kevinmfox/8-bit-computer/images/alu01.jpg

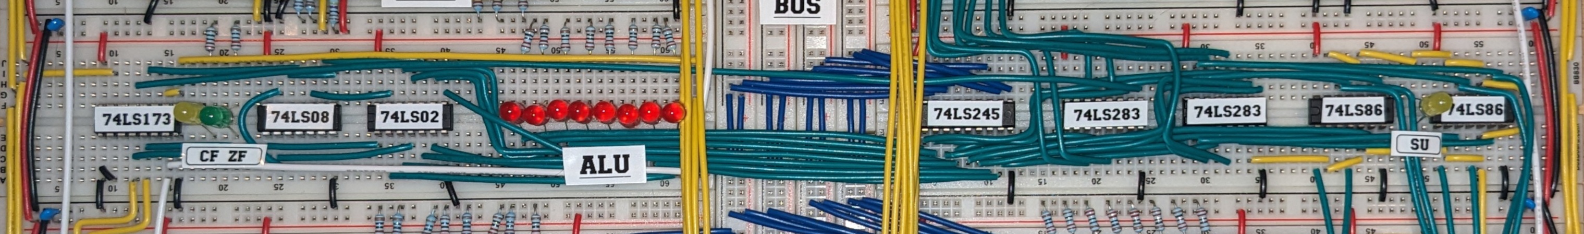
images/alu01.jpg
