kevinmfox/8-bit-computer/images/alu_and_flags01.jpg

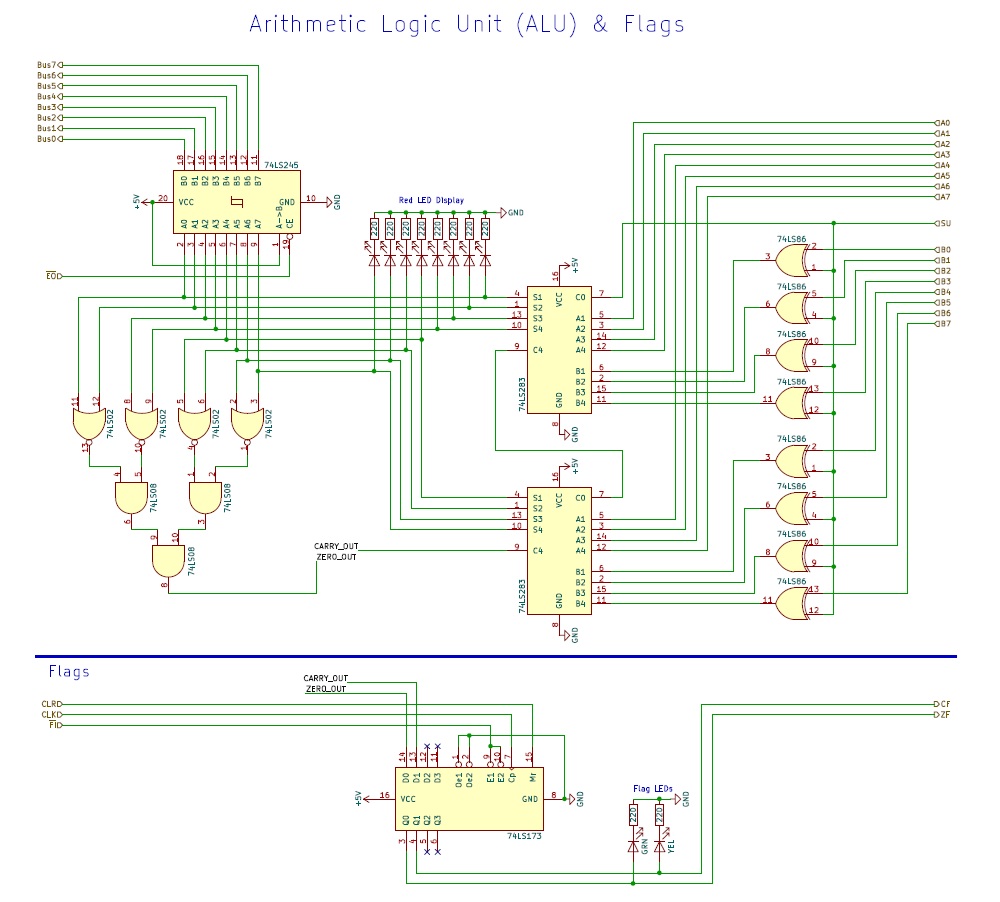
images/alu_and_flags01.jpg
