kevinmfox/8-bit-computer/images/alu_full01.jpg

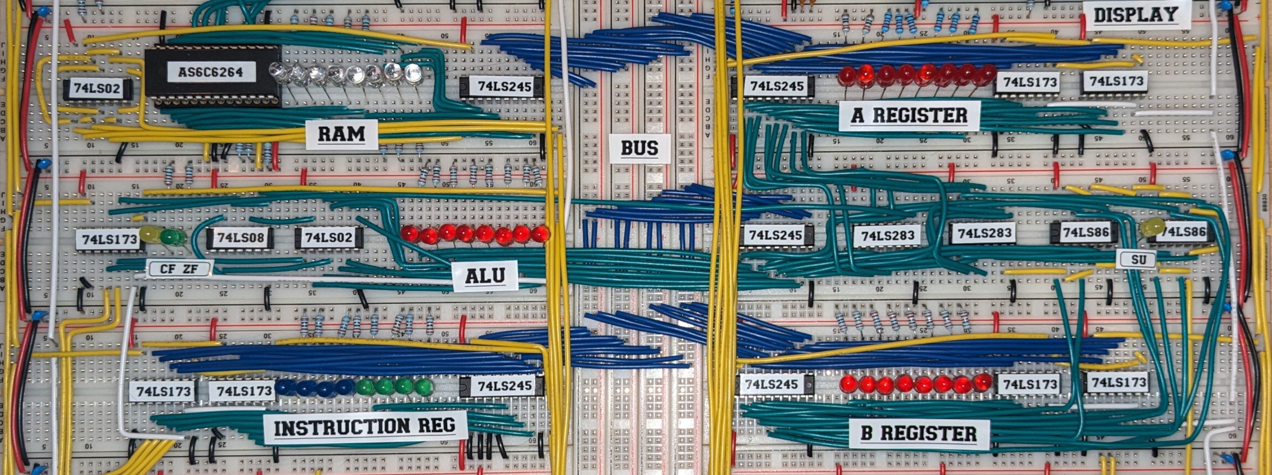
images/alu_full01.jpg
