kevinmfox/8-bit-computer/images/alu_left01.jpg

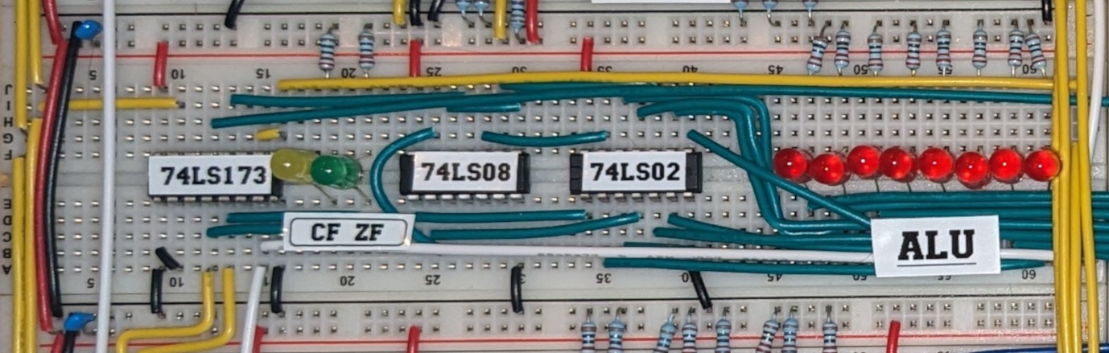
images/alu_left01.jpg
