kevinmfox/8-bit-computer/images/alu_right01.jpg

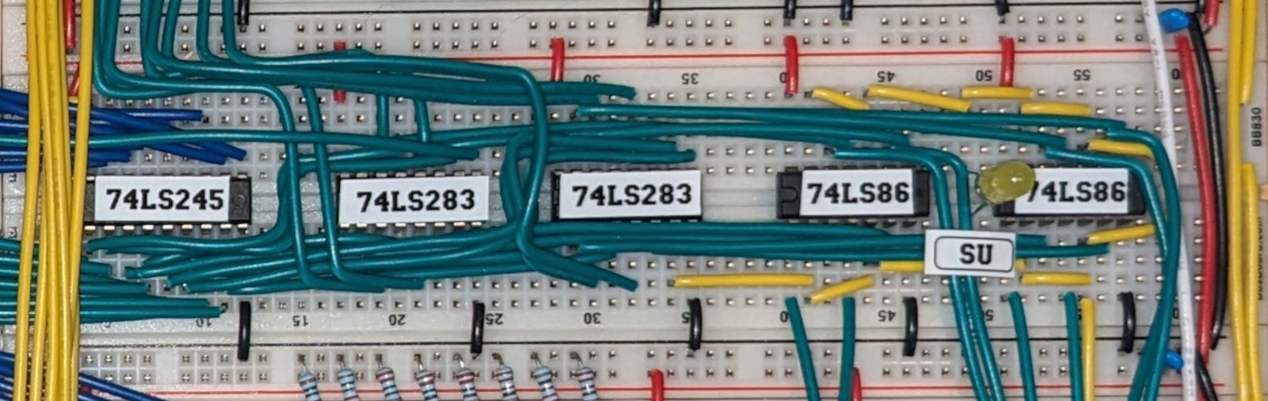
images/alu_right01.jpg
