kevinmfox/8-bit-computer/images/clock01.jpg

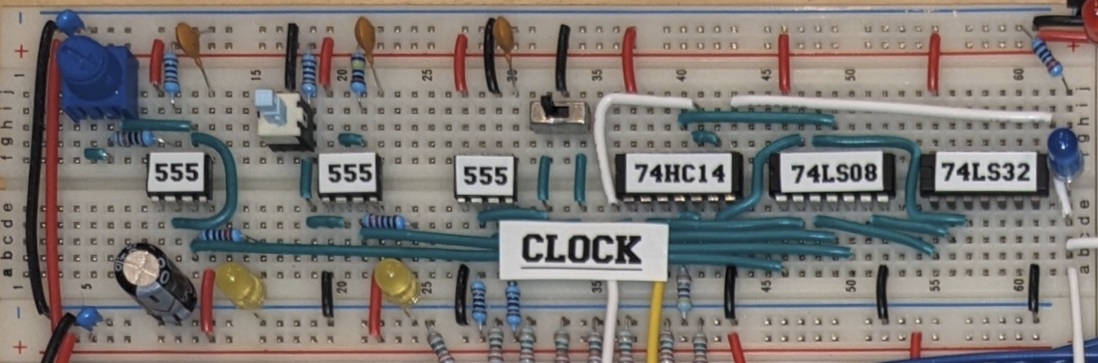
images/clock01.jpg
