kevinmfox/8-bit-computer/images/control01.jpg

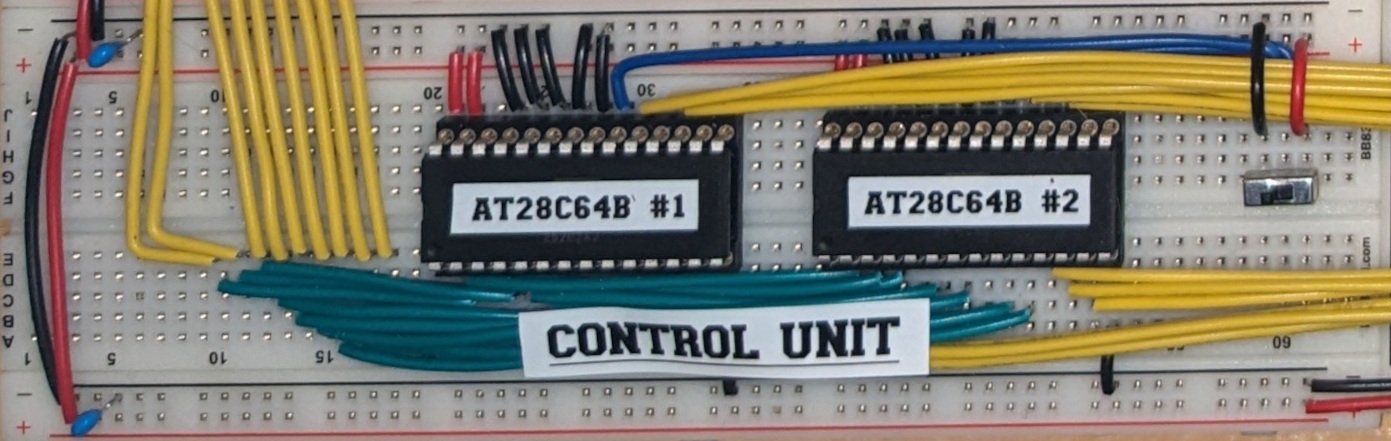
images/control01.jpg
