kevinmfox/8-bit-computer/images/control_leds01.jpg

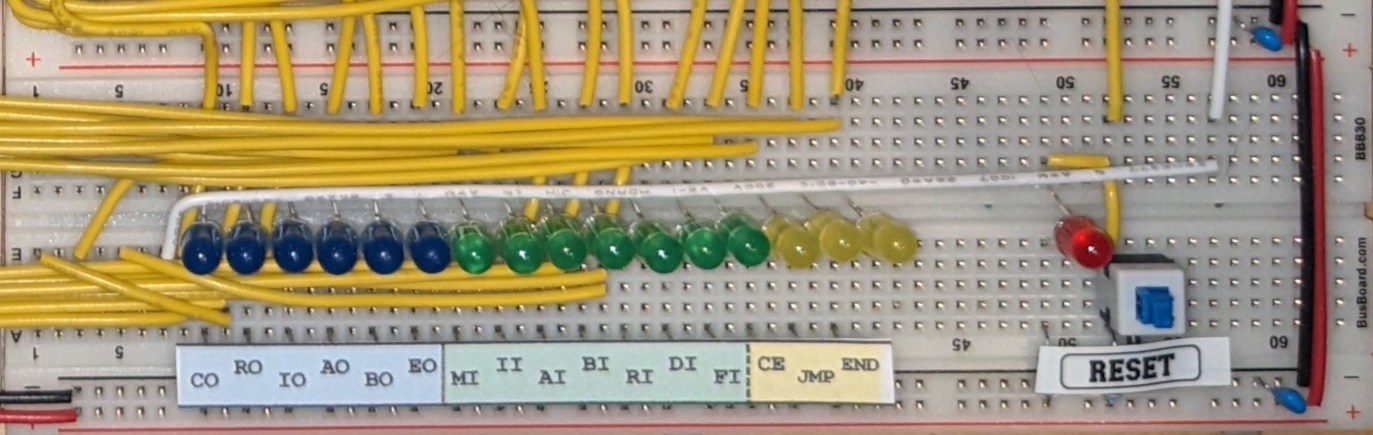
images/control_leds01.jpg
