kevinmfox/8-bit-computer/images/display01.jpg

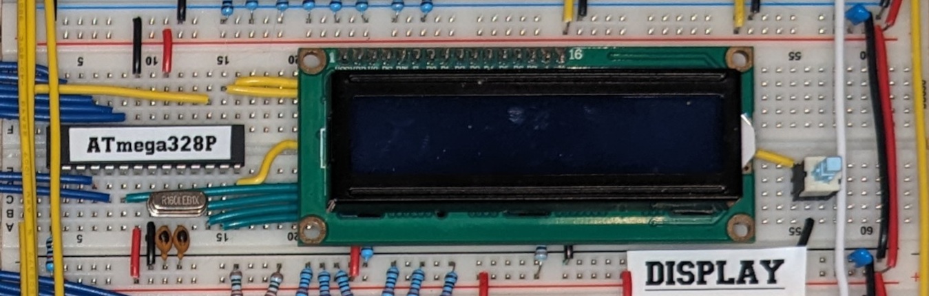
images/display01.jpg
