kevinmfox/8-bit-computer/images/display04.jpg

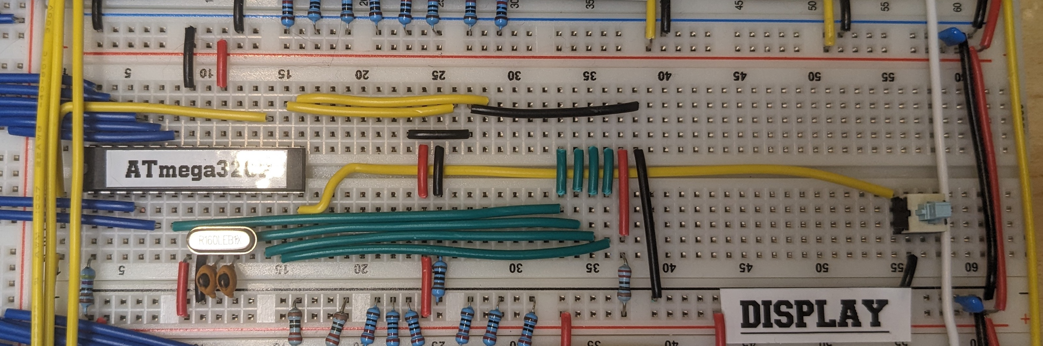
images/display04.jpg
