kevinmfox/8-bit-computer/images/ir01.jpg

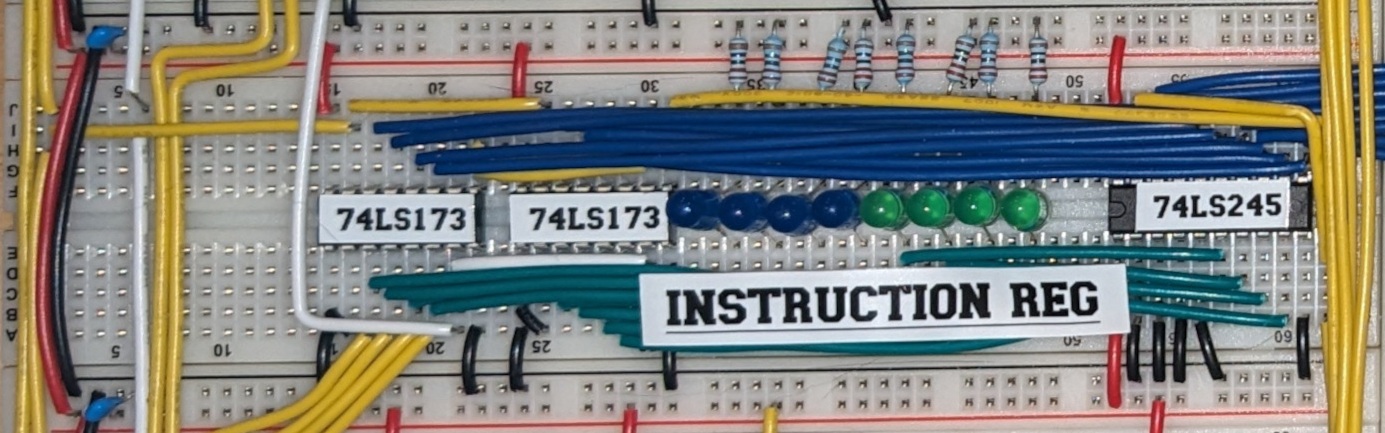
images/ir01.jpg
