kevinmfox/8-bit-computer/images/mar01.jpg

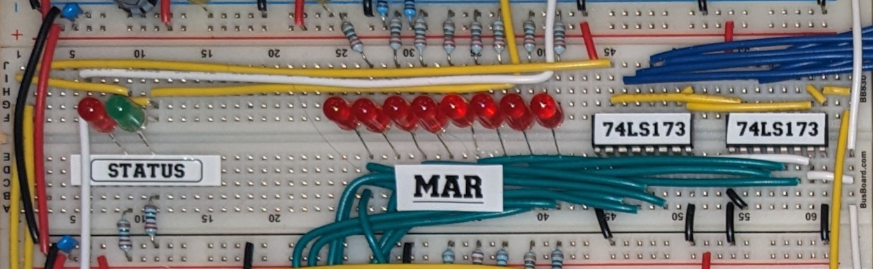
images/mar01.jpg
