kevinmfox/8-bit-computer/images/ram01.jpg

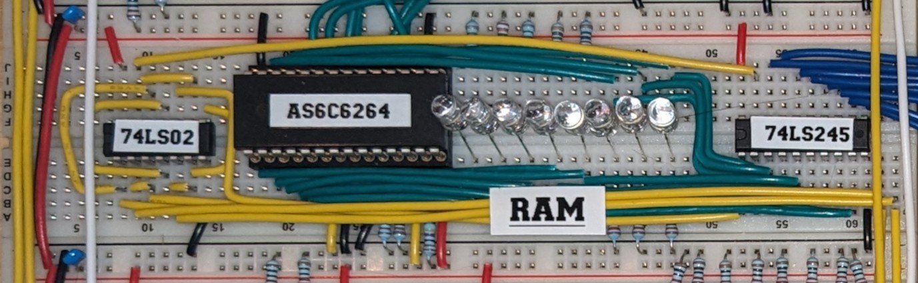
images/ram01.jpg
