kevinmfox/8-bit-computer/images/ram_programmer_sch01.jpg

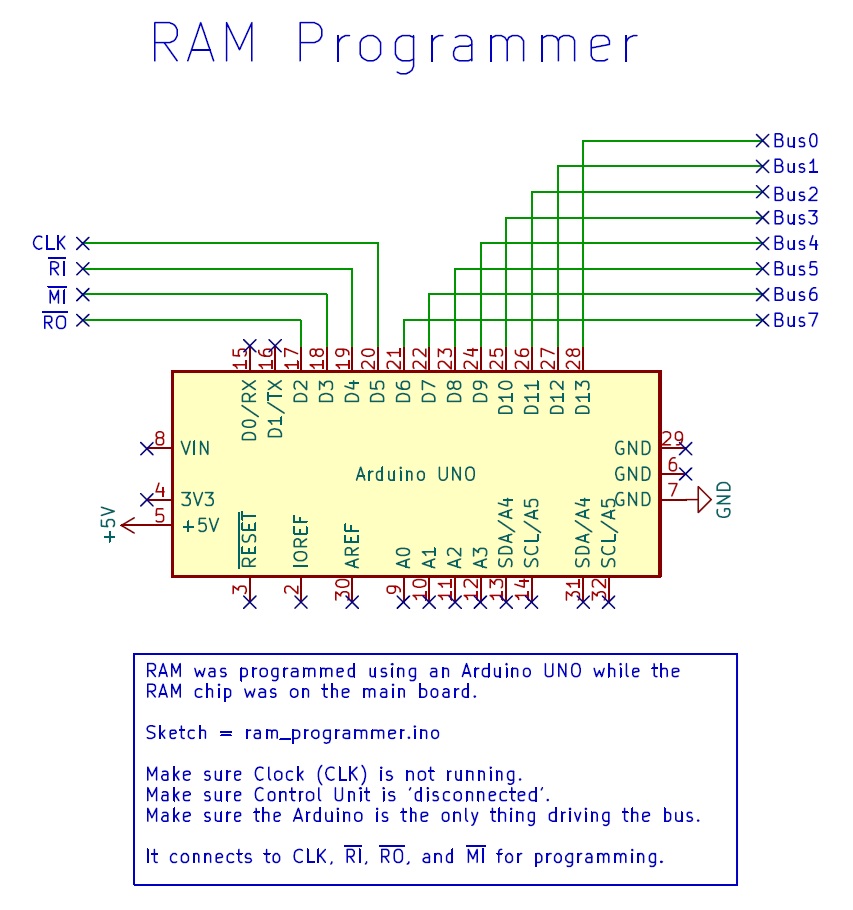
images/ram_programmer_sch01.jpg
