kevinmfox/8-bit-computer/images/build02.jpg

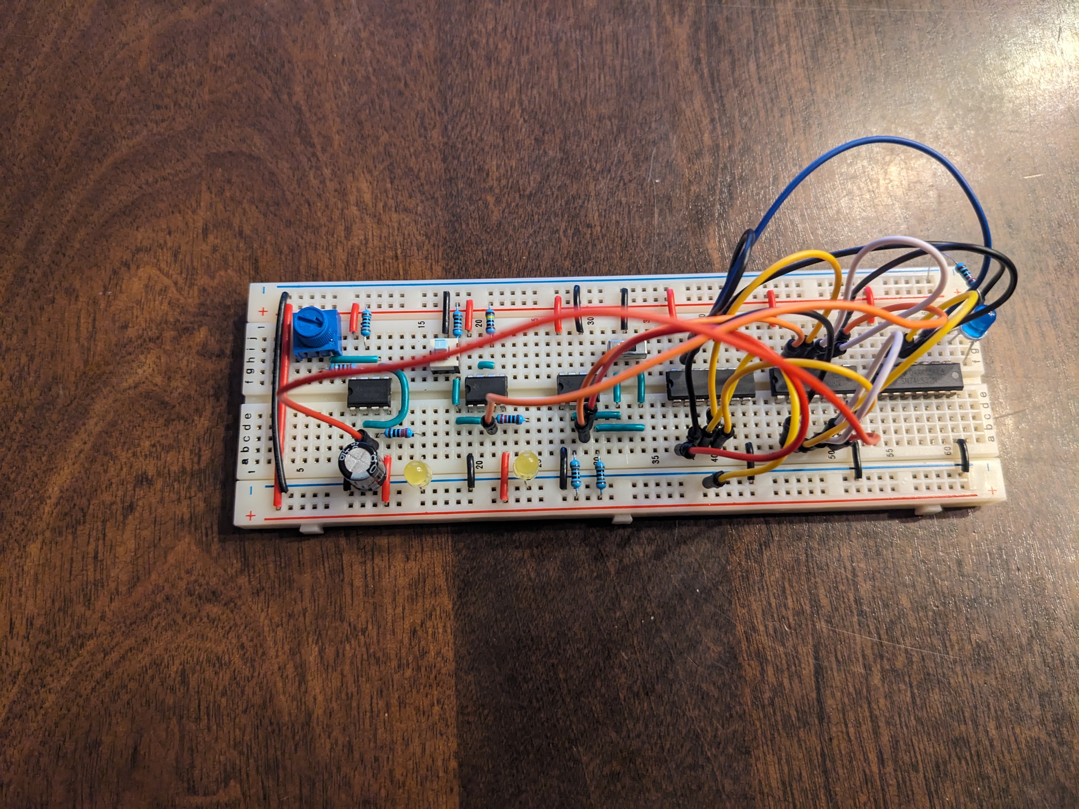
images/build02.jpg
