kevinmfox/8-bit-computer/images/build10.jpg

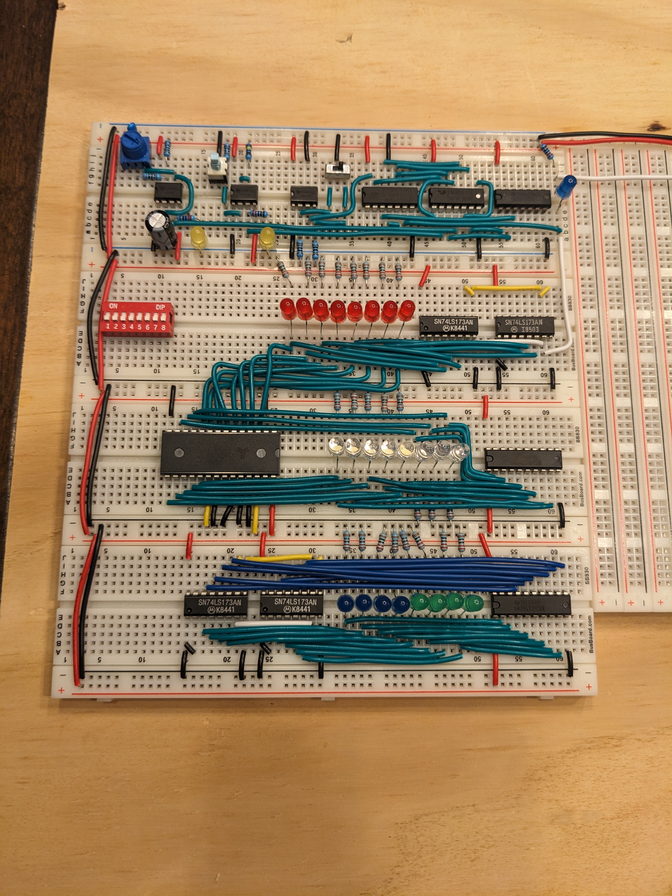
images/build10.jpg
