kevinmfox/8-bit-computer/images/build12.jpg

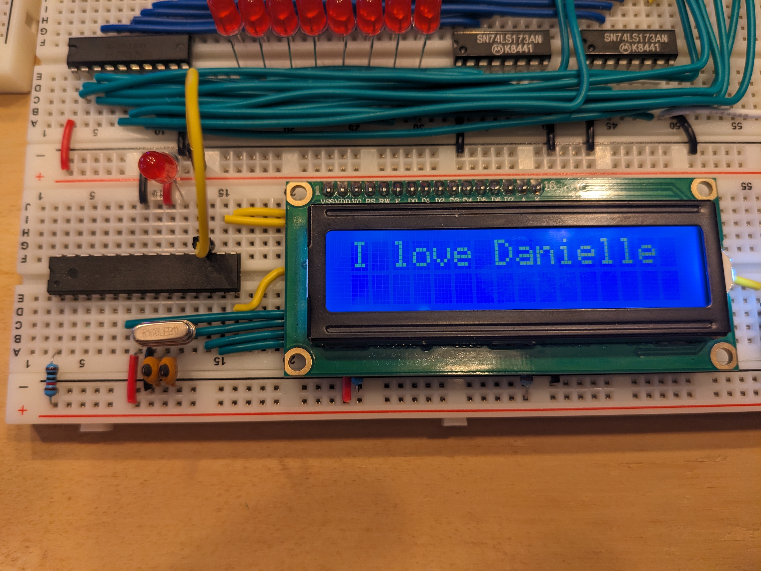
images/build12.jpg
