kevinmfox/8-bit-computer/images/build13.jpg

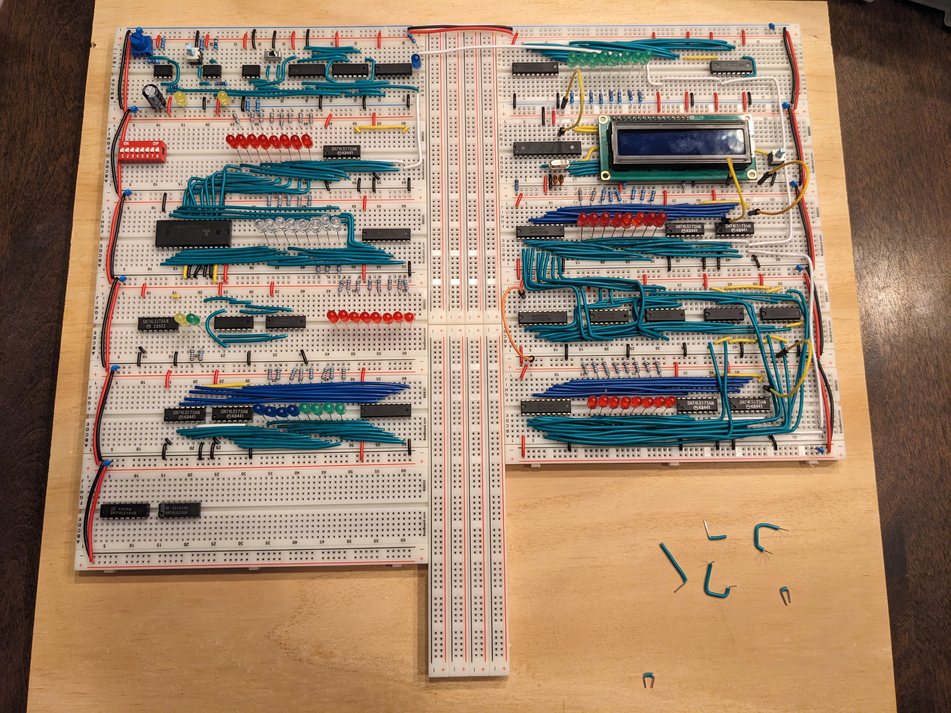
images/build13.jpg
