kevinmfox/8-bit-computer/schematics/Main/main.kicad_sch

## KiCad design schematics/Main/main.kicad_sch (2026-01-15)

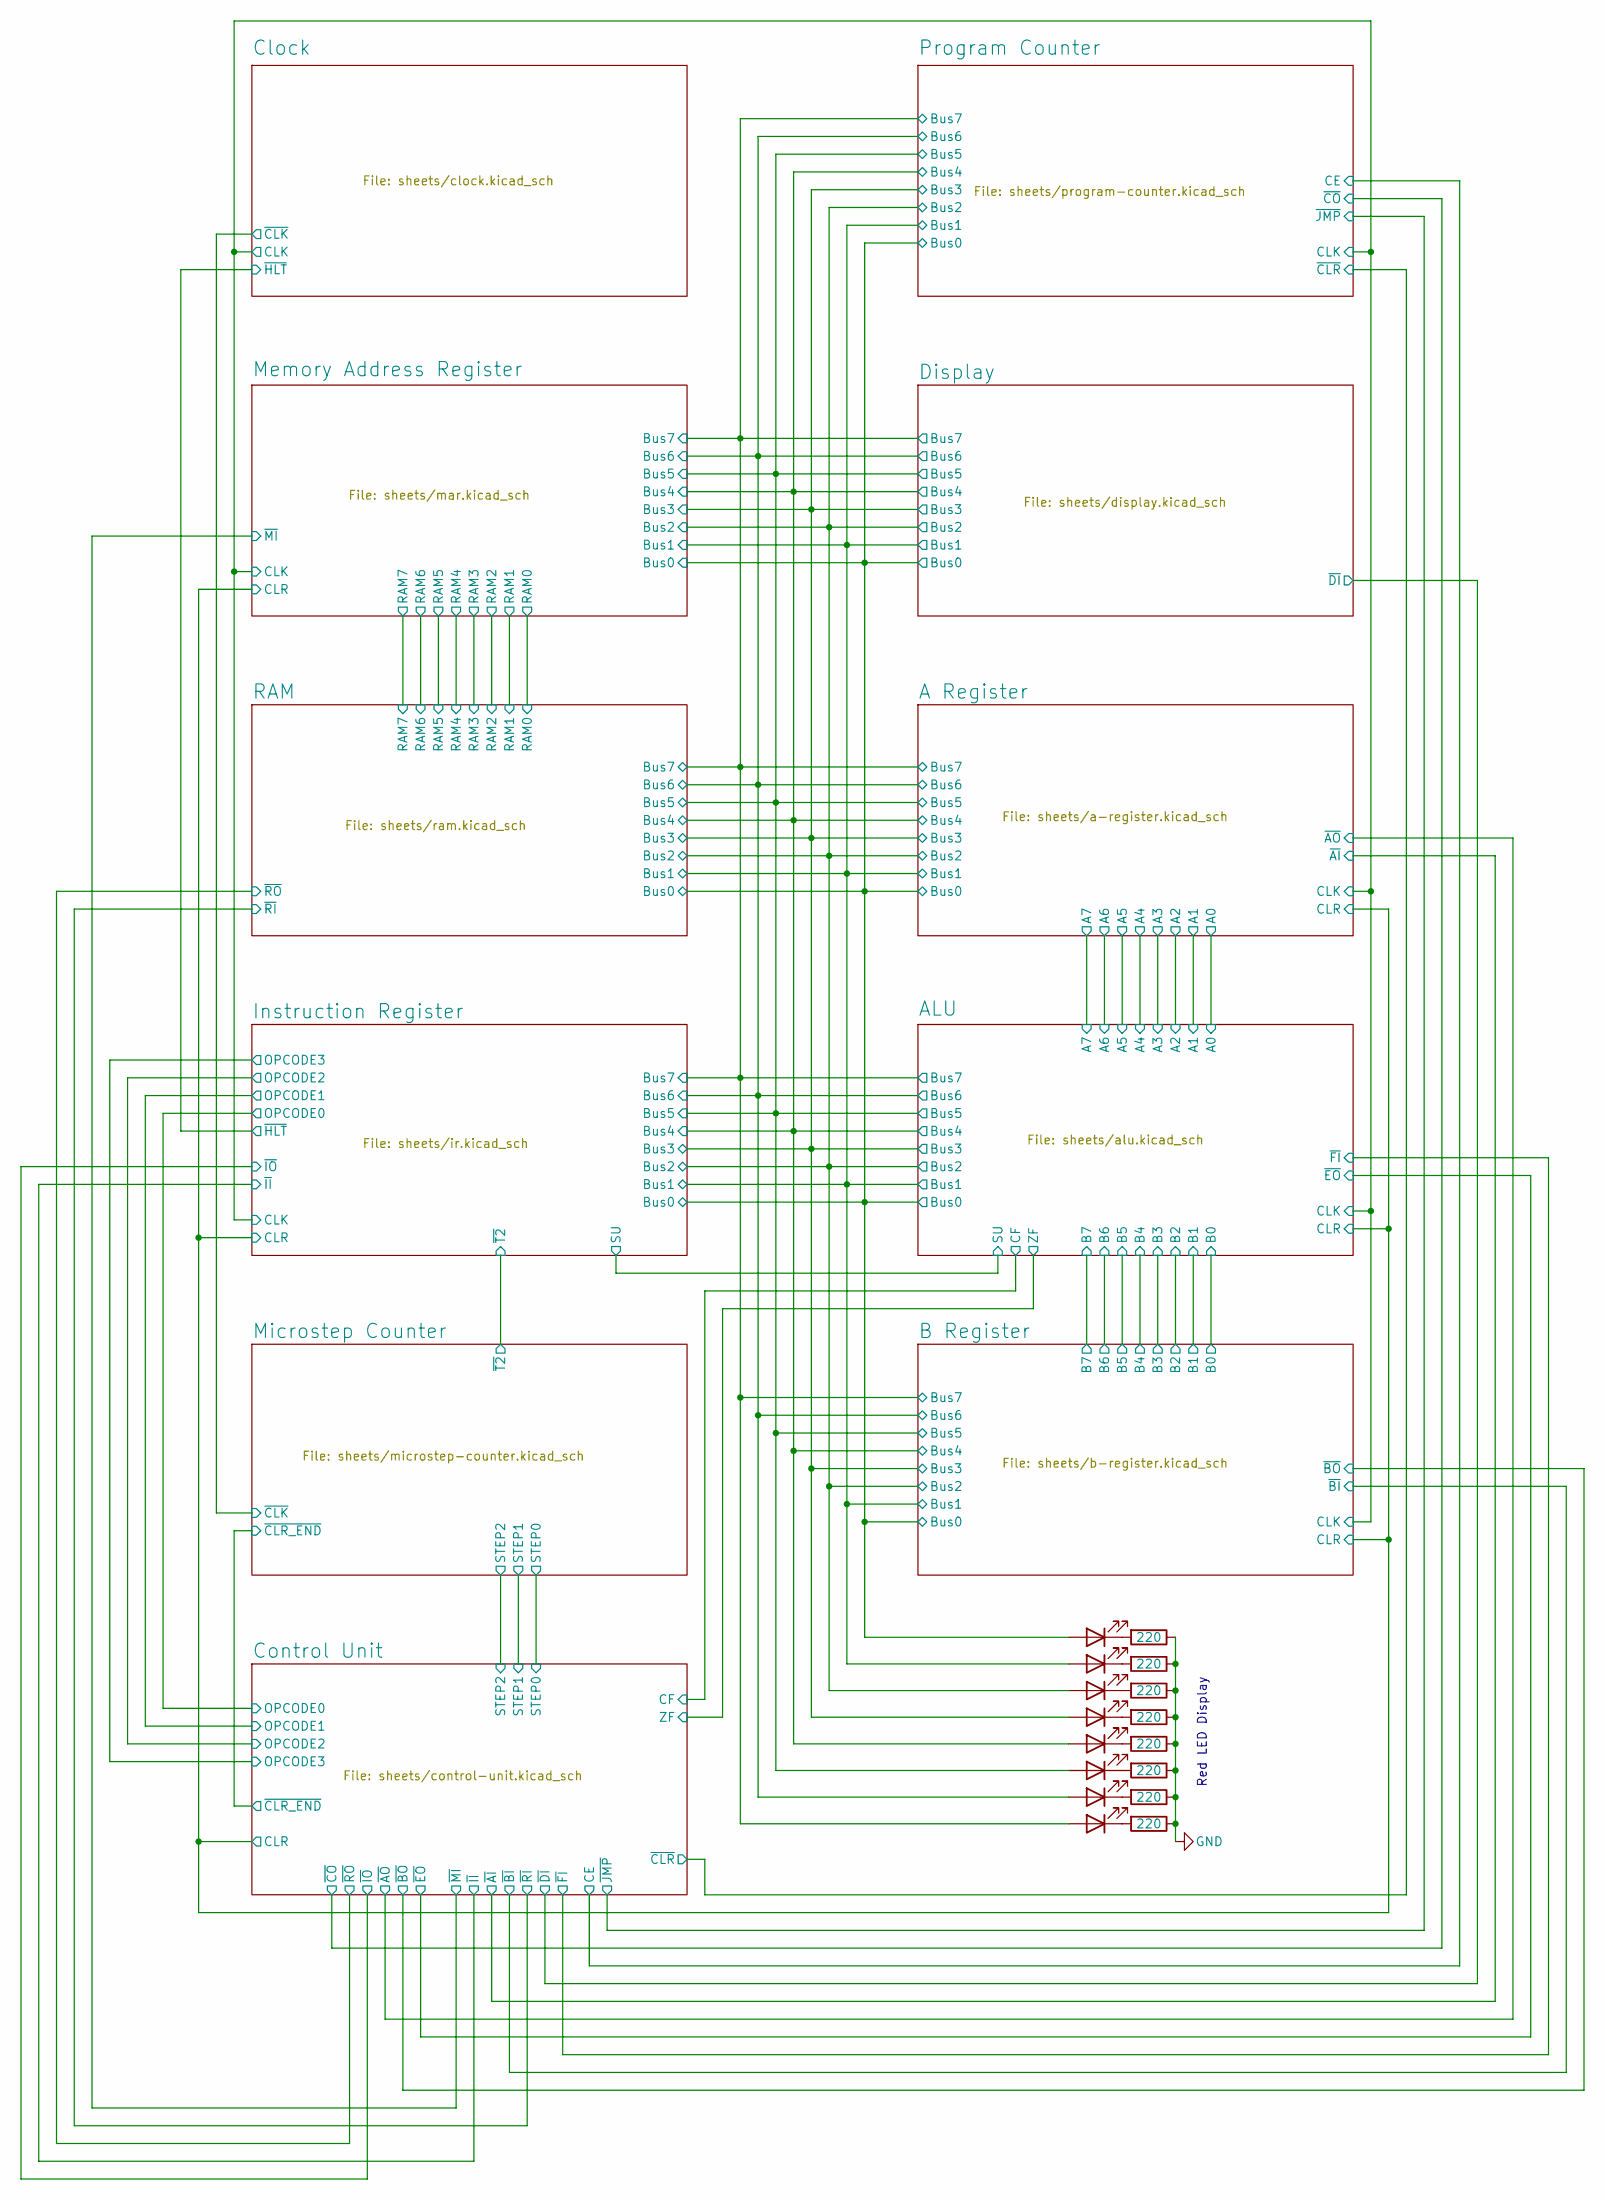
[picture p75: schematic main.kicad_sch]

Parts:
D85, D86, D87, D88, D89, D90, D91, D92: RED; LED_D5.0mm
R97, R98, R99, R100, R101, R102, R103, R104: 220; R_Axial_DIN0207_L6.3mm_D2.5mm_P7.62mm_Horizontal

Connections:
Bus0: D92.2 (A)
Bus1: D91.2 (A)
Bus2: D90.2 (A)
Bus3: D89.2 (A)
Bus4: D88.2 (A)
Bus5: D87.2 (A)
Bus6: D86.2 (A)
Bus7: D85.2 (A)
GND: R97.1, R98.1, R99.1, R100.1, R101.1, R102.1, R103.1, R104.1
unnamed: D85.1 (K), R97.2
unnamed: D86.1 (K), R98.2
unnamed: D87.1 (K), R99.2
unnamed: D88.1 (K), R100.2
unnamed: D89.1 (K), R101.2
unnamed: D90.1 (K), R102.2
unnamed: D91.1 (K), R103.2
unnamed: D92.1 (K), R104.2

Notes on the sheet:
Red LED Display
