kevinmfox/8-bit-computer/schematics/Tooling/EEPROM Programmer.kicad_sch

## KiCad design schematics/Tooling/EEPROM Programmer.kicad_sch (2026-01-15)

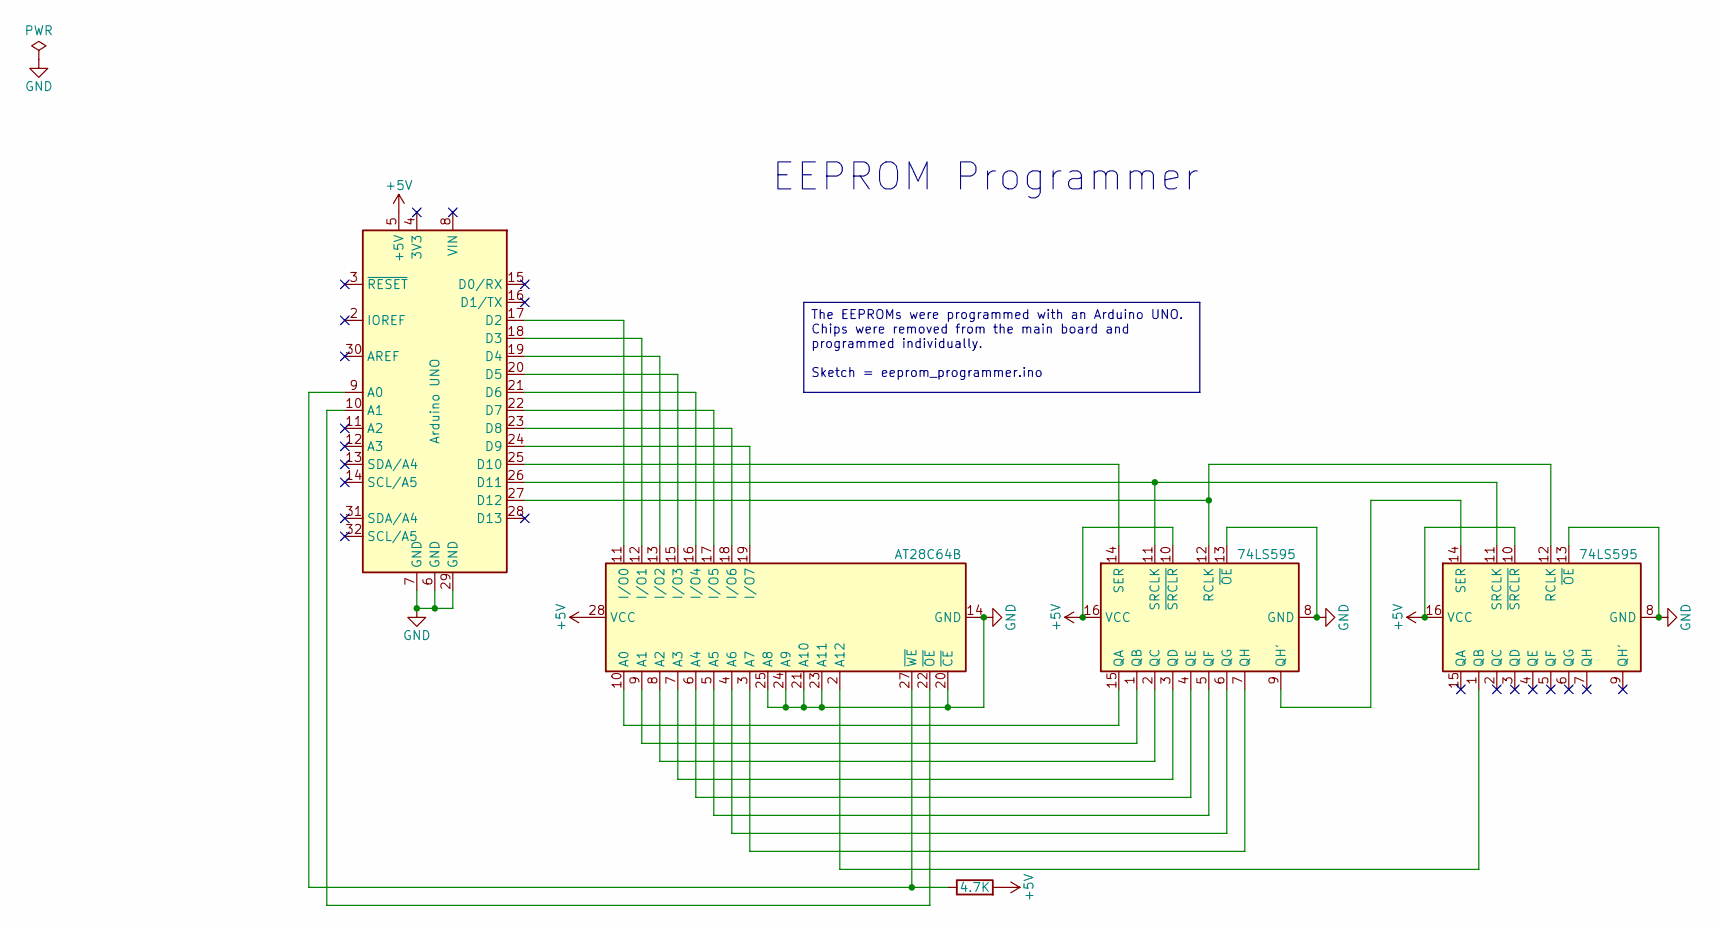
[picture p76: schematic EEPROM Programmer.kicad_sch]

Parts:
A1: Arduino UNO; Arduino_UNO_R3
R1: 4.7K
U1, U3: 74LS595
U2: AT28C64B; DIP-28_W15.24mm

Connections:
+5V: A1.5 (+5V), R1.2, U1.10 (~SRCLR), U1.16 (VCC), U2.28 (VCC), U3.10 (~SRCLR), U3.16 (VCC)
GND: A1.6 (GND), A1.7 (GND), A1.29 (GND), U1.8 (GND), U1.13 (~OE), U2.14 (GND), U2.20 (~CE), U2.21 (A10), U2.23 (A11), U2.24 (A9), U2.25 (A8), U3.8 (GND), U3.13 (~OE)
unnamed: A1.9 (A0), R1.1, U2.27 (~WE)
unnamed: A1.10 (A1), U2.22 (~OE)
unnamed: A1.17 (D2), U2.11 (I/O0)
unnamed: A1.18 (D3), U2.12 (I/O1)
unnamed: A1.19 (D4), U2.13 (I/O2)
unnamed: A1.20 (D5), U2.15 (I/O3)
unnamed: A1.21 (D6), U2.16 (I/O4)
unnamed: A1.22 (D7), U2.17 (I/O5)
unnamed: A1.23 (D8), U2.18 (I/O6)
unnamed: A1.24 (D9), U2.19 (I/O7)
unnamed: A1.25 (D10), U3.14 (SER)
unnamed: A1.26 (D11), U1.11 (SRCLK), U3.11 (SRCLK)
unnamed: A1.27 (D12), U1.12 (RCLK), U3.12 (RCLK)
unnamed: U1.1 (QB), U2.2 (A12)
unnamed: U1.14 (SER), U3.9 (QH')
unnamed: U2.3 (A7), U3.7 (QH)
unnamed: U2.4 (A6), U3.6 (QG)
unnamed: U2.5 (A5), U3.5 (QF)
unnamed: U2.6 (A4), U3.4 (QE)
unnamed: U2.7 (A3), U3.3 (QD)
unnamed: U2.8 (A2), U3.2 (QC)
unnamed: U2.9 (A1), U3.1 (QB)
unnamed: U2.10 (A0), U3.15 (QA)

Notes on the sheet:
EEPROM Programmer
The EEPROMs were programmed with an Arduino UNO. Chips were removed from the main board and programmed individually. Sketch = eeprom_programmer.ino
