kevinmfox/8-bit-computer/schematics/Main/sheets/a-register.kicad_sch

## KiCad design schematics/Main/sheets/a-register.kicad_sch (2026-01-15)

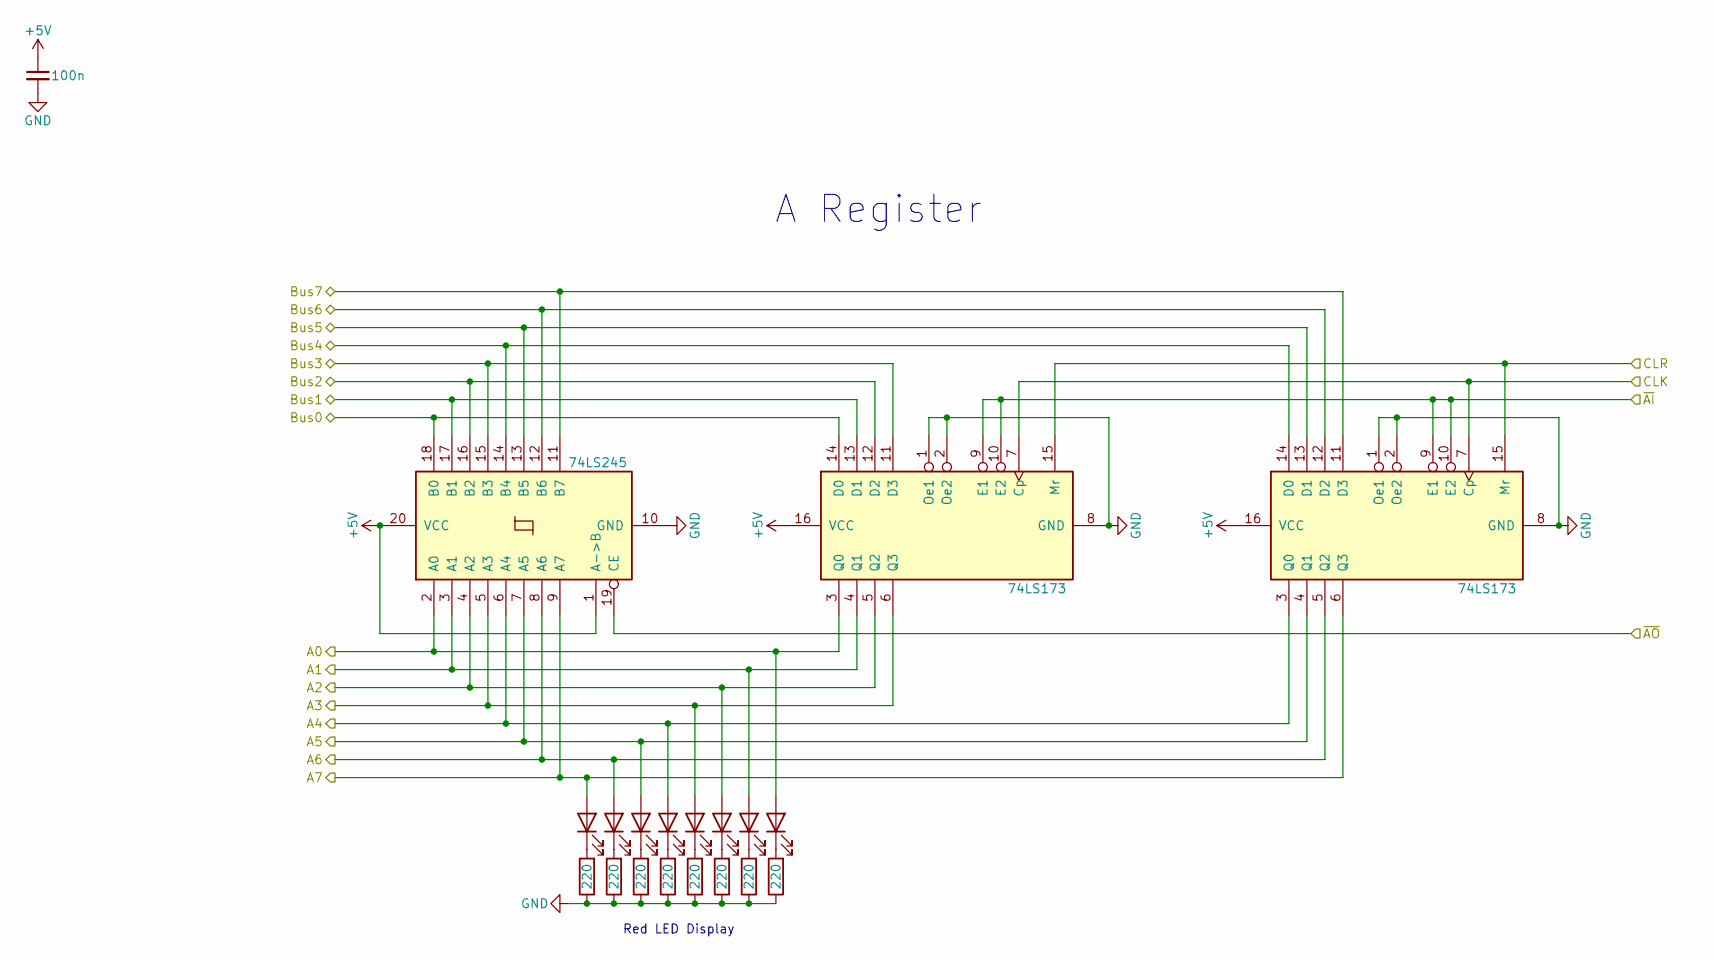
[picture p77: schematic a-register.kicad_sch]

Parts:
C8: 100n; C_Disc_D5.0mm_W2.5mm_P5.00mm
D20, D21, D22, D23, D24, D25, D26, D27: RED; LED_D5.0mm
R26, R27, R28, R29, R30, R31, R32, R33: 220; R_Axial_DIN0207_L6.3mm_D2.5mm_P7.62mm_Horizontal
U9: 74LS245; DIP-22_W7.62mm_Socket_LongPads
U10, U11: 74LS173; DIP-16_W7.62mm_Socket_LongPads

Connections:
+5V: C8.1, U9.1 (A->B), U9.20 (VCC), U10.16 (VCC), U11.16 (VCC)
A0: D27.2 (A), U9.2 (A0), U10.3 (Q0)
A1: D26.2 (A), U9.3 (A1), U10.4 (Q1)
A2: D25.2 (A), U9.4 (A2), U10.5 (Q2)
A3: D24.2 (A), U9.5 (A3), U10.6 (Q3)
A4: D23.2 (A), U9.6 (A4), U11.3 (Q0)
A5: D22.2 (A), U9.7 (A5), U11.4 (Q1)
A6: D21.2 (A), U9.8 (A6), U11.5 (Q2)
A7: D20.2 (A), U9.9 (A7), U11.6 (Q3)
Bus0: U9.18 (B0), U10.14 (D0)
Bus1: U9.17 (B1), U10.13 (D1)
Bus2: U9.16 (B2), U10.12 (D2)
Bus3: U9.15 (B3), U10.11 (D3)
Bus4: U9.14 (B4), U11.14 (D0)
Bus5: U9.13 (B5), U11.13 (D1)
Bus6: U9.12 (B6), U11.12 (D2)
Bus7: U9.11 (B7), U11.11 (D3)
CLK: U10.7 (Cp), U11.7 (Cp)
CLR: U10.15 (Mr), U11.15 (Mr)
GND: C8.2, R26.1, R27.1, R28.1, R29.1, R30.1, R31.1, R32.1, R33.1, U9.10 (GND), U10.1 (Oe1), U10.2 (Oe2), U10.8 (GND), U11.1 (Oe1), U11.2 (Oe2), U11.8 (GND)
unnamed: D20.1 (K), R26.2
unnamed: D21.1 (K), R27.2
unnamed: D22.1 (K), R28.2
unnamed: D23.1 (K), R29.2
unnamed: D24.1 (K), R30.2
unnamed: D25.1 (K), R31.2
unnamed: D26.1 (K), R32.2
unnamed: D27.1 (K), R33.2
~AI: U10.9 (E1), U10.10 (E2), U11.9 (E1), U11.10 (E2)
~AO: U9.19 (CE)

Notes on the sheet:
A Register
Red LED Display
