kevinmfox/8-bit-computer/schematics/Main/sheets/alu.kicad_sch

## KiCad design schematics/Main/sheets/alu.kicad_sch (2026-01-15)

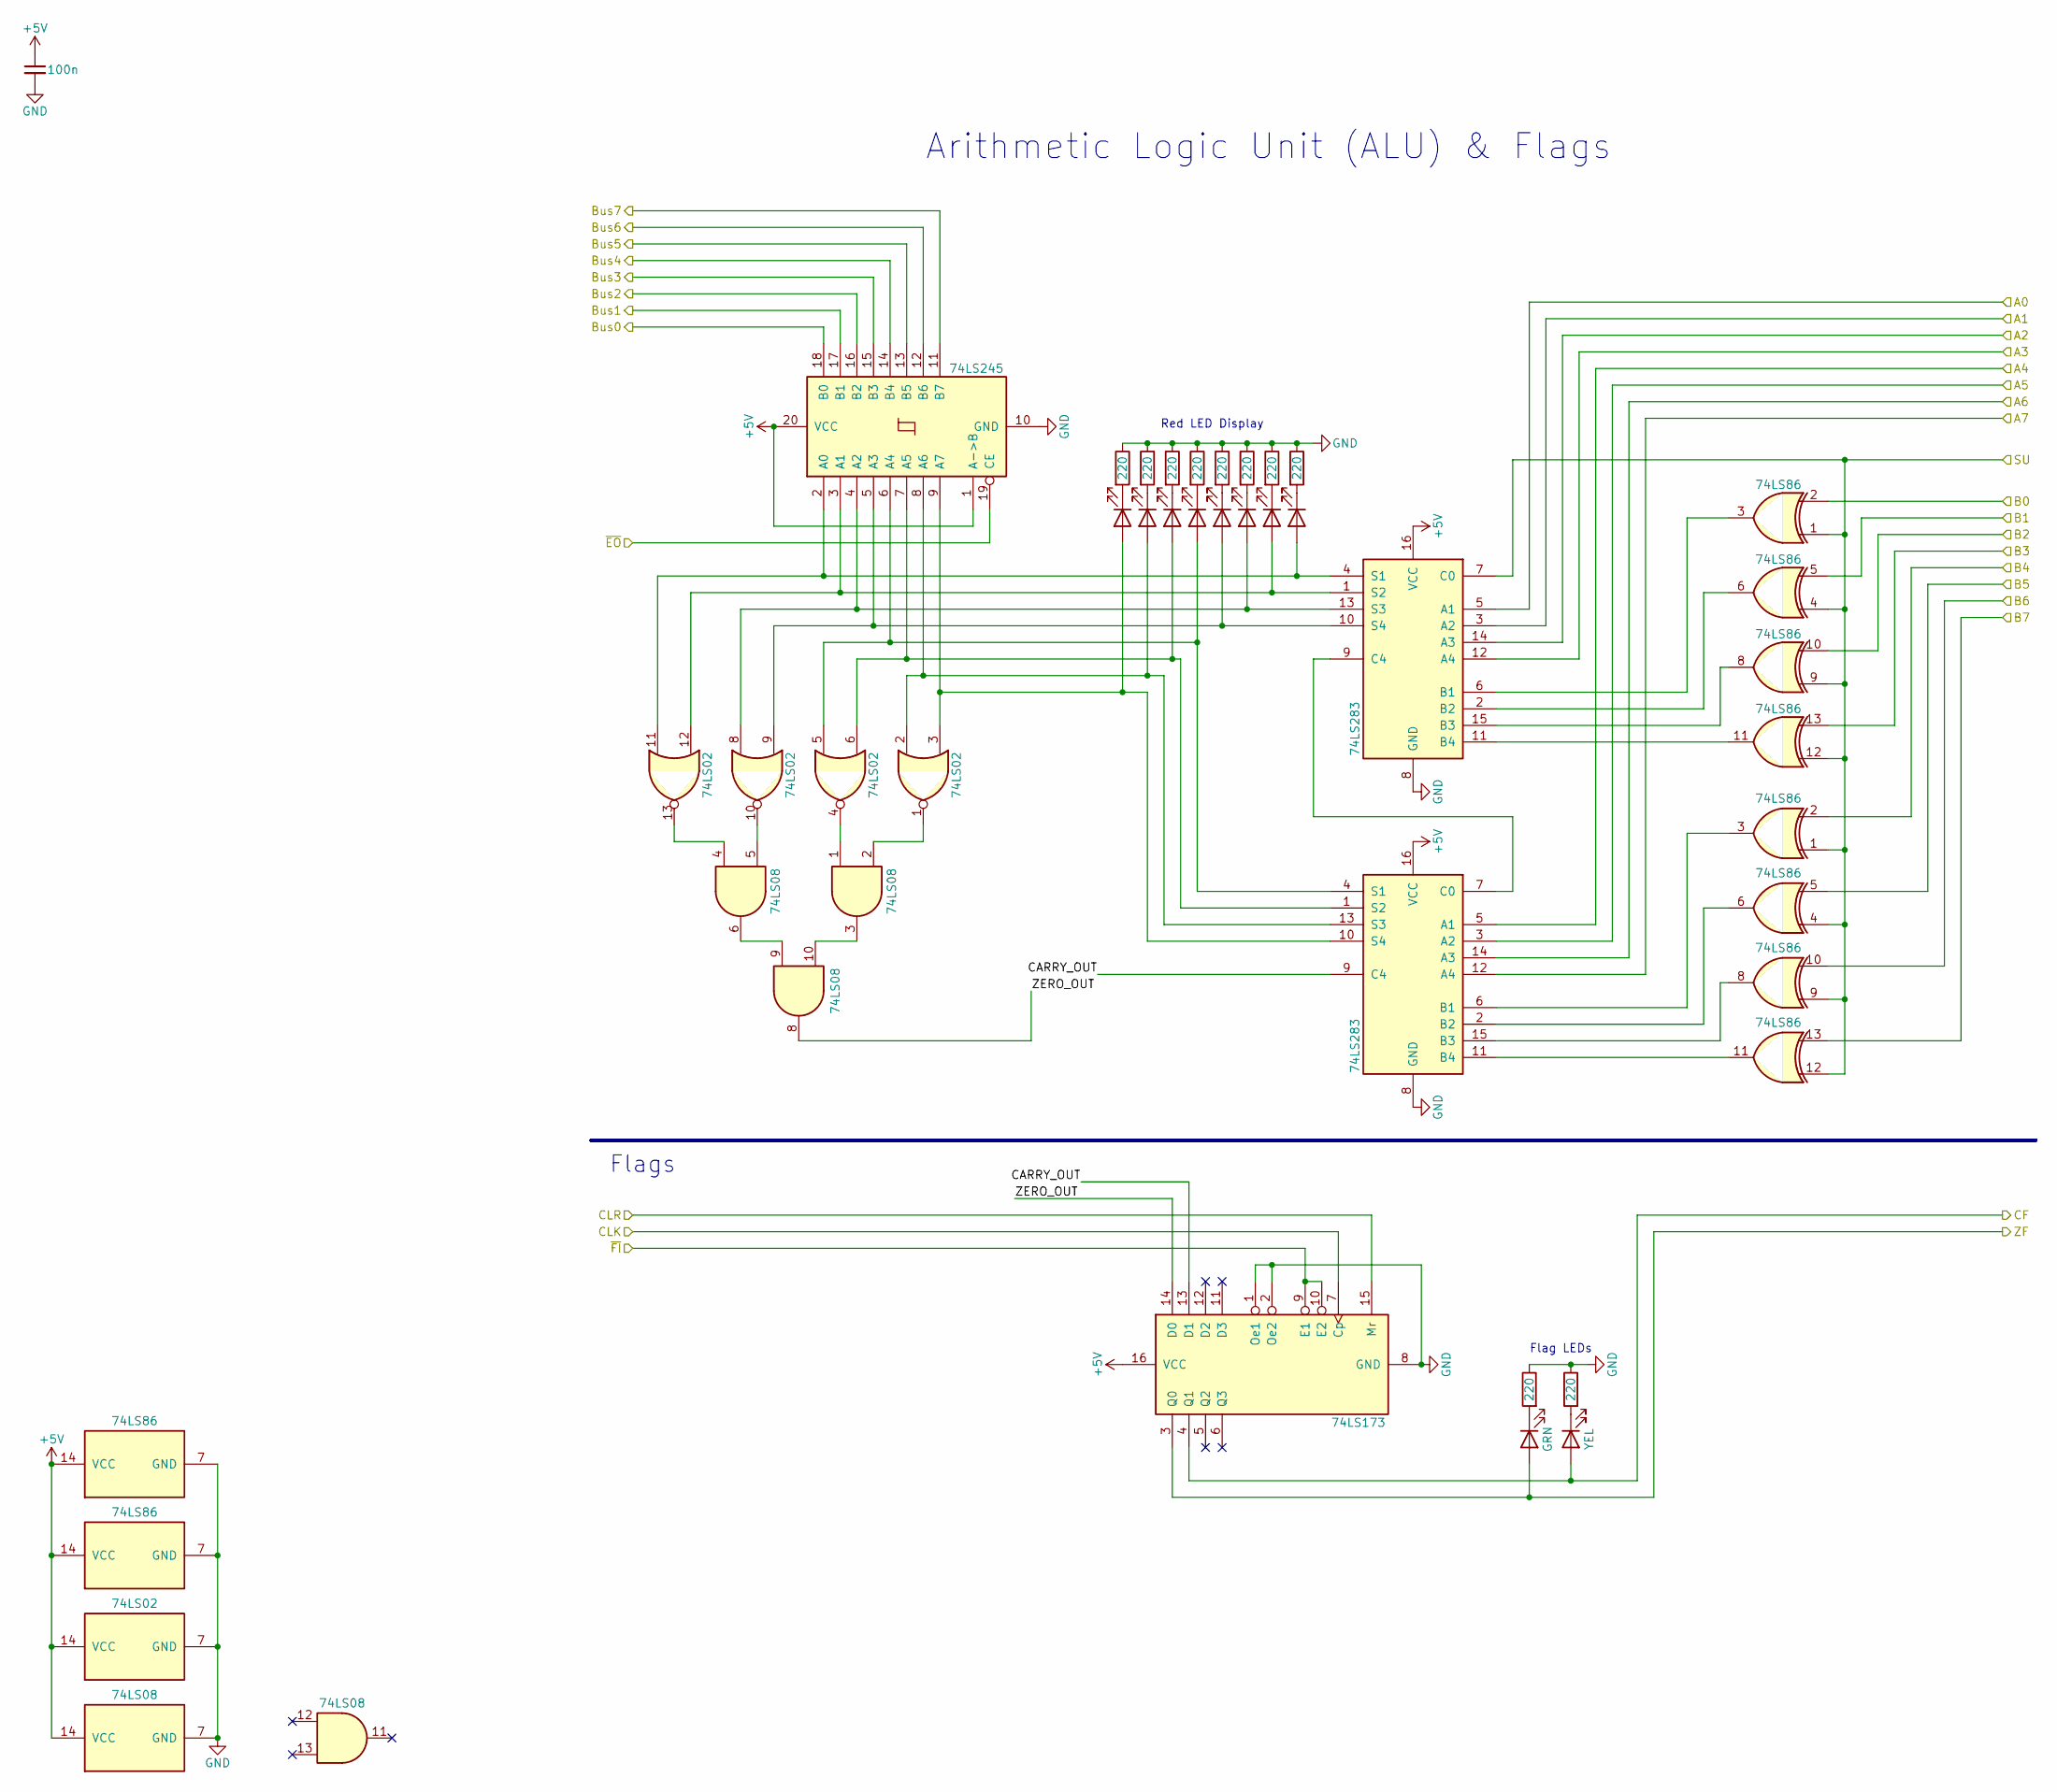
[picture p78: schematic alu.kicad_sch]

Parts:
C10: 100n; C_Disc_D5.0mm_W2.5mm_P5.00mm
D59, D60, D61, D62, D63, D64, D65, D82: RED; LED_D5.0mm
D83: YEL; LED_D5.0mm
D84: GRN; LED_D5.0mm
R71, R72, R73, R74, R75, R76, R93, R94, R95, R96: 220; R_Axial_DIN0207_L6.3mm_D2.5mm_P7.62mm_Horizontal
U31: 74LS173; DIP-16_W7.62mm_Socket_LongPads
U32: 74LS245; DIP-22_W7.62mm_Socket_LongPads
U33, U34: 74LS283; DIP-16_W7.62mm_Socket_LongPads
U35, U36: 74LS86; DIP-14_W7.62mm_Socket_LongPads
U37: 74LS02; DIP-14_W7.62mm_Socket_LongPads
U38: 74LS08; DIP-14_W7.62mm_Socket_LongPads

Connections:
+5V: C10.1, U31.16 (VCC), U32.1 (A->B), U32.20 (VCC), U33.16 (VCC), U34.16 (VCC), U35.14 (VCC), U36.14 (VCC), U37.14 (VCC), U38.14 (VCC)
A0: U33.5 (A1)
A1: U33.3 (A2)
A2: U33.14 (A3)
A3: U33.12 (A4)
A4: U34.5 (A1)
A5: U34.3 (A2)
A6: U34.14 (A3)
A7: U34.12 (A4)
B0: U35.2
B1: U35.5
B2: U35.10
B3: U35.13
B4: U36.2
B5: U36.5
B6: U36.10
B7: U36.13
Bus0: U32.18 (B0)
Bus1: U32.17 (B1)
Bus2: U32.16 (B2)
Bus3: U32.15 (B3)
Bus4: U32.14 (B4)
Bus5: U32.13 (B5)
Bus6: U32.12 (B6)
Bus7: U32.11 (B7)
CARRY_OUT: U31.13 (D1), U34.9 (C4)
CF: D83.2 (A), U31.4 (Q1)
CLK: U31.7 (Cp)
CLR: U31.15 (Mr)
GND: C10.2, R71.1, R72.1, R73.1, R74.1, R75.1, R76.1, R93.1, R94.1, R95.1, R96.1, U31.1 (Oe1), U31.2 (Oe2), U31.8 (GND), U32.10 (GND), U33.8 (GND), U34.8 (GND), U35.7 (GND), U36.7 (GND), U37.7 (GND), U38.7 (GND)
unnamed: D59.1 (K), R71.2
unnamed: D59.2 (A), U32.2 (A0), U33.4 (S1), U37.11
unnamed: D60.1 (K), R72.2
unnamed: D60.2 (A), U32.3 (A1), U33.1 (S2), U37.12
unnamed: D61.1 (K), R73.2
unnamed: D61.2 (A), U32.4 (A2), U33.13 (S3), U37.8
unnamed: D62.1 (K), R74.2
unnamed: D62.2 (A), U32.5 (A3), U33.10 (S4), U37.9
unnamed: D63.1 (K), R75.2
unnamed: D63.2 (A), U32.6 (A4), U34.4 (S1), U37.5
unnamed: D64.1 (K), R76.2
unnamed: D64.2 (A), U32.7 (A5), U34.1 (S2), U37.6
unnamed: D65.1 (K), R93.2
unnamed: D65.2 (A), U32.8 (A6), U34.13 (S3), U37.2
unnamed: D82.1 (K), R94.2
unnamed: D82.2 (A), U32.9 (A7), U34.10 (S4), U37.3
unnamed: D83.1 (K), R96.2
unnamed: D84.1 (K), R95.2
unnamed: U33.2 (B2), U35.6
unnamed: U33.6 (B1), U35.3
unnamed: U33.9 (C4), U34.7 (C0)
unnamed: U33.11 (B4), U35.11
unnamed: U33.15 (B3), U35.8
unnamed: U34.2 (B2), U36.6
unnamed: U34.6 (B1), U36.3
unnamed: U34.11 (B4), U36.11
unnamed: U34.15 (B3), U36.8
unnamed: U37.1, U38.2
unnamed: U37.4, U38.1
unnamed: U37.10, U38.5
unnamed: U37.13, U38.4
unnamed: U38.6, U38.9
unnamed: U38.3, U38.10
SU: U33.7 (C0), U35.1, U35.4, U35.9, U35.12, U36.1, U36.4, U36.9, U36.12
ZERO_OUT: U31.14 (D0), U38.8
ZF: D84.2 (A), U31.3 (Q0)
~EO: U32.19 (CE)
~FI: U31.9 (E1), U31.10 (E2)

Notes on the sheet:
Red LED Display
Flags
Arithmetic Logic Unit (ALU) & Flags
Flag LEDs
