kevinmfox/8-bit-computer/schematics/Main/sheets/b-register.kicad_sch

## KiCad design schematics/Main/sheets/b-register.kicad_sch (2026-01-15)

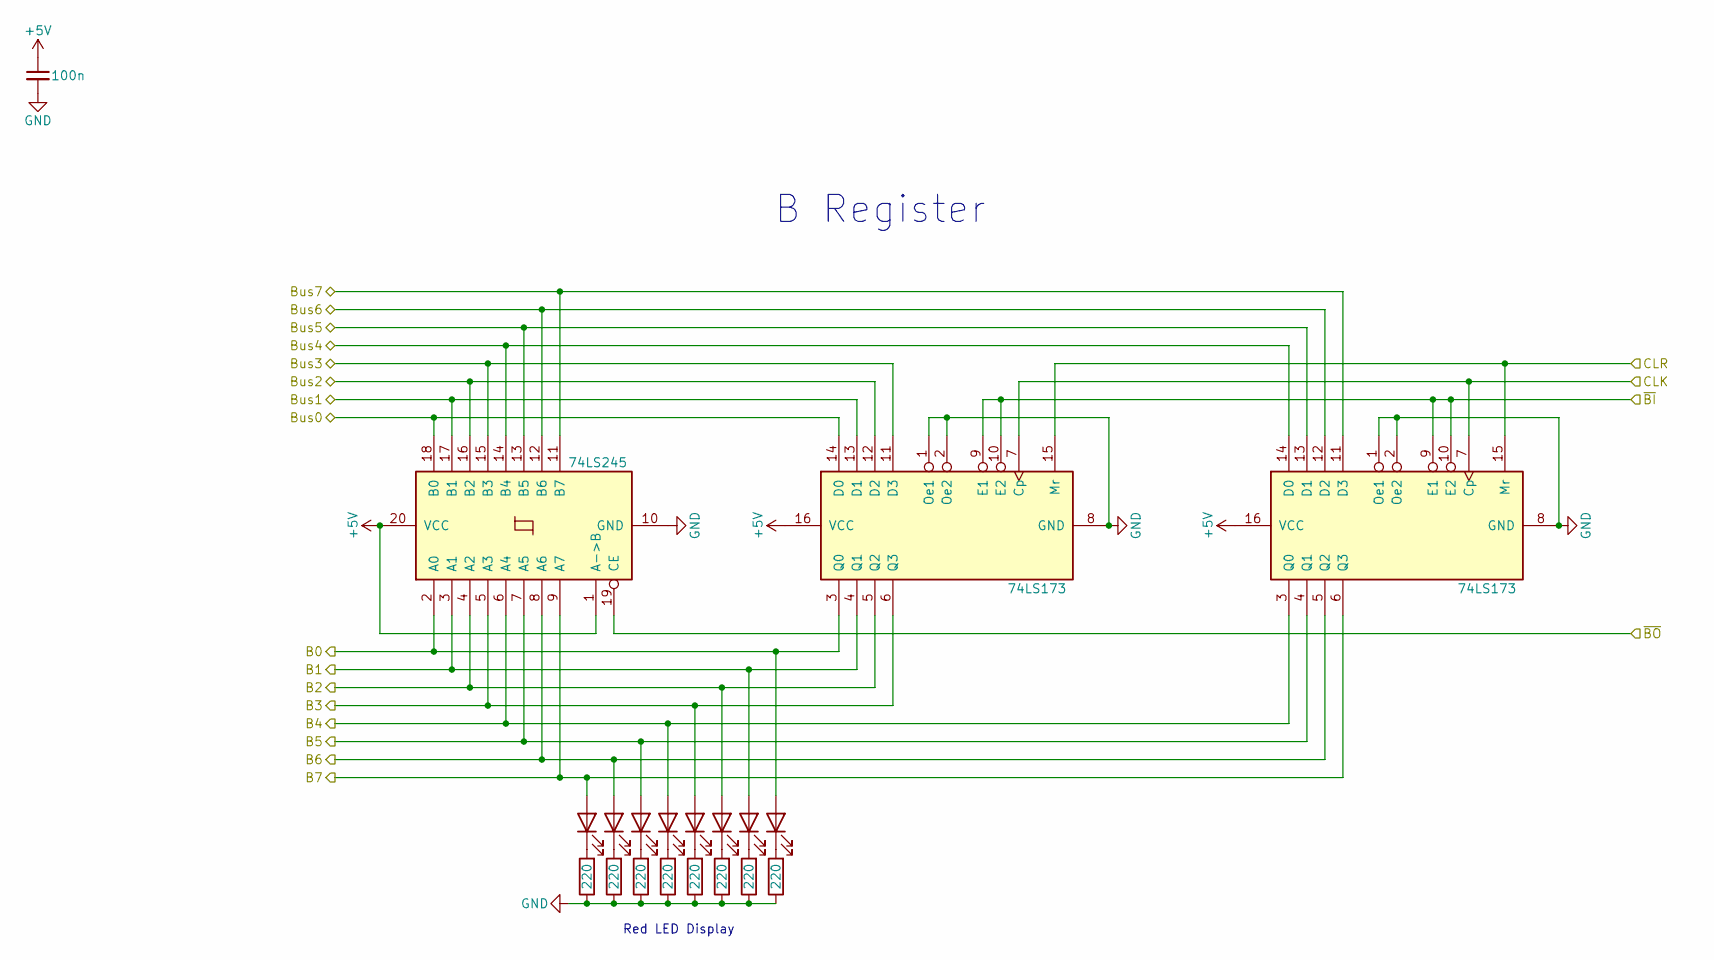
[picture p79: schematic b-register.kicad_sch]

Parts:
C9: 100n; C_Disc_D5.0mm_W2.5mm_P5.00mm
D28, D29, D30, D31, D32, D33, D34, D35: RED; LED_D5.0mm
R34, R35, R36, R37, R38, R39, R40, R41: 220; R_Axial_DIN0207_L6.3mm_D2.5mm_P7.62mm_Horizontal
U12: 74LS245; DIP-22_W7.62mm_Socket_LongPads
U13, U14: 74LS173; DIP-16_W7.62mm_Socket_LongPads

Connections:
+5V: C9.1, U12.1 (A->B), U12.20 (VCC), U13.16 (VCC), U14.16 (VCC)
B0: D35.2 (A), U12.2 (A0), U13.3 (Q0)
B1: D34.2 (A), U12.3 (A1), U13.4 (Q1)
B2: D33.2 (A), U12.4 (A2), U13.5 (Q2)
B3: D32.2 (A), U12.5 (A3), U13.6 (Q3)
B4: D31.2 (A), U12.6 (A4), U14.3 (Q0)
B5: D30.2 (A), U12.7 (A5), U14.4 (Q1)
B6: D29.2 (A), U12.8 (A6), U14.5 (Q2)
B7: D28.2 (A), U12.9 (A7), U14.6 (Q3)
Bus0: U12.18 (B0), U13.14 (D0)
Bus1: U12.17 (B1), U13.13 (D1)
Bus2: U12.16 (B2), U13.12 (D2)
Bus3: U12.15 (B3), U13.11 (D3)
Bus4: U12.14 (B4), U14.14 (D0)
Bus5: U12.13 (B5), U14.13 (D1)
Bus6: U12.12 (B6), U14.12 (D2)
Bus7: U12.11 (B7), U14.11 (D3)
CLK: U13.7 (Cp), U14.7 (Cp)
CLR: U13.15 (Mr), U14.15 (Mr)
GND: C9.2, R34.1, R35.1, R36.1, R37.1, R38.1, R39.1, R40.1, R41.1, U12.10 (GND), U13.1 (Oe1), U13.2 (Oe2), U13.8 (GND), U14.1 (Oe1), U14.2 (Oe2), U14.8 (GND)
unnamed: D28.1 (K), R34.2
unnamed: D29.1 (K), R35.2
unnamed: D30.1 (K), R36.2
unnamed: D31.1 (K), R37.2
unnamed: D32.1 (K), R38.2
unnamed: D33.1 (K), R39.2
unnamed: D34.1 (K), R40.2
unnamed: D35.1 (K), R41.2
~BI: U13.9 (E1), U13.10 (E2), U14.9 (E1), U14.10 (E2)
~BO: U12.19 (CE)

Notes on the sheet:
Red LED Display
B Register
