kevinmfox/8-bit-computer/schematics/Main/sheets/clock.kicad_sch

## KiCad design schematics/Main/sheets/clock.kicad_sch (2026-01-15)

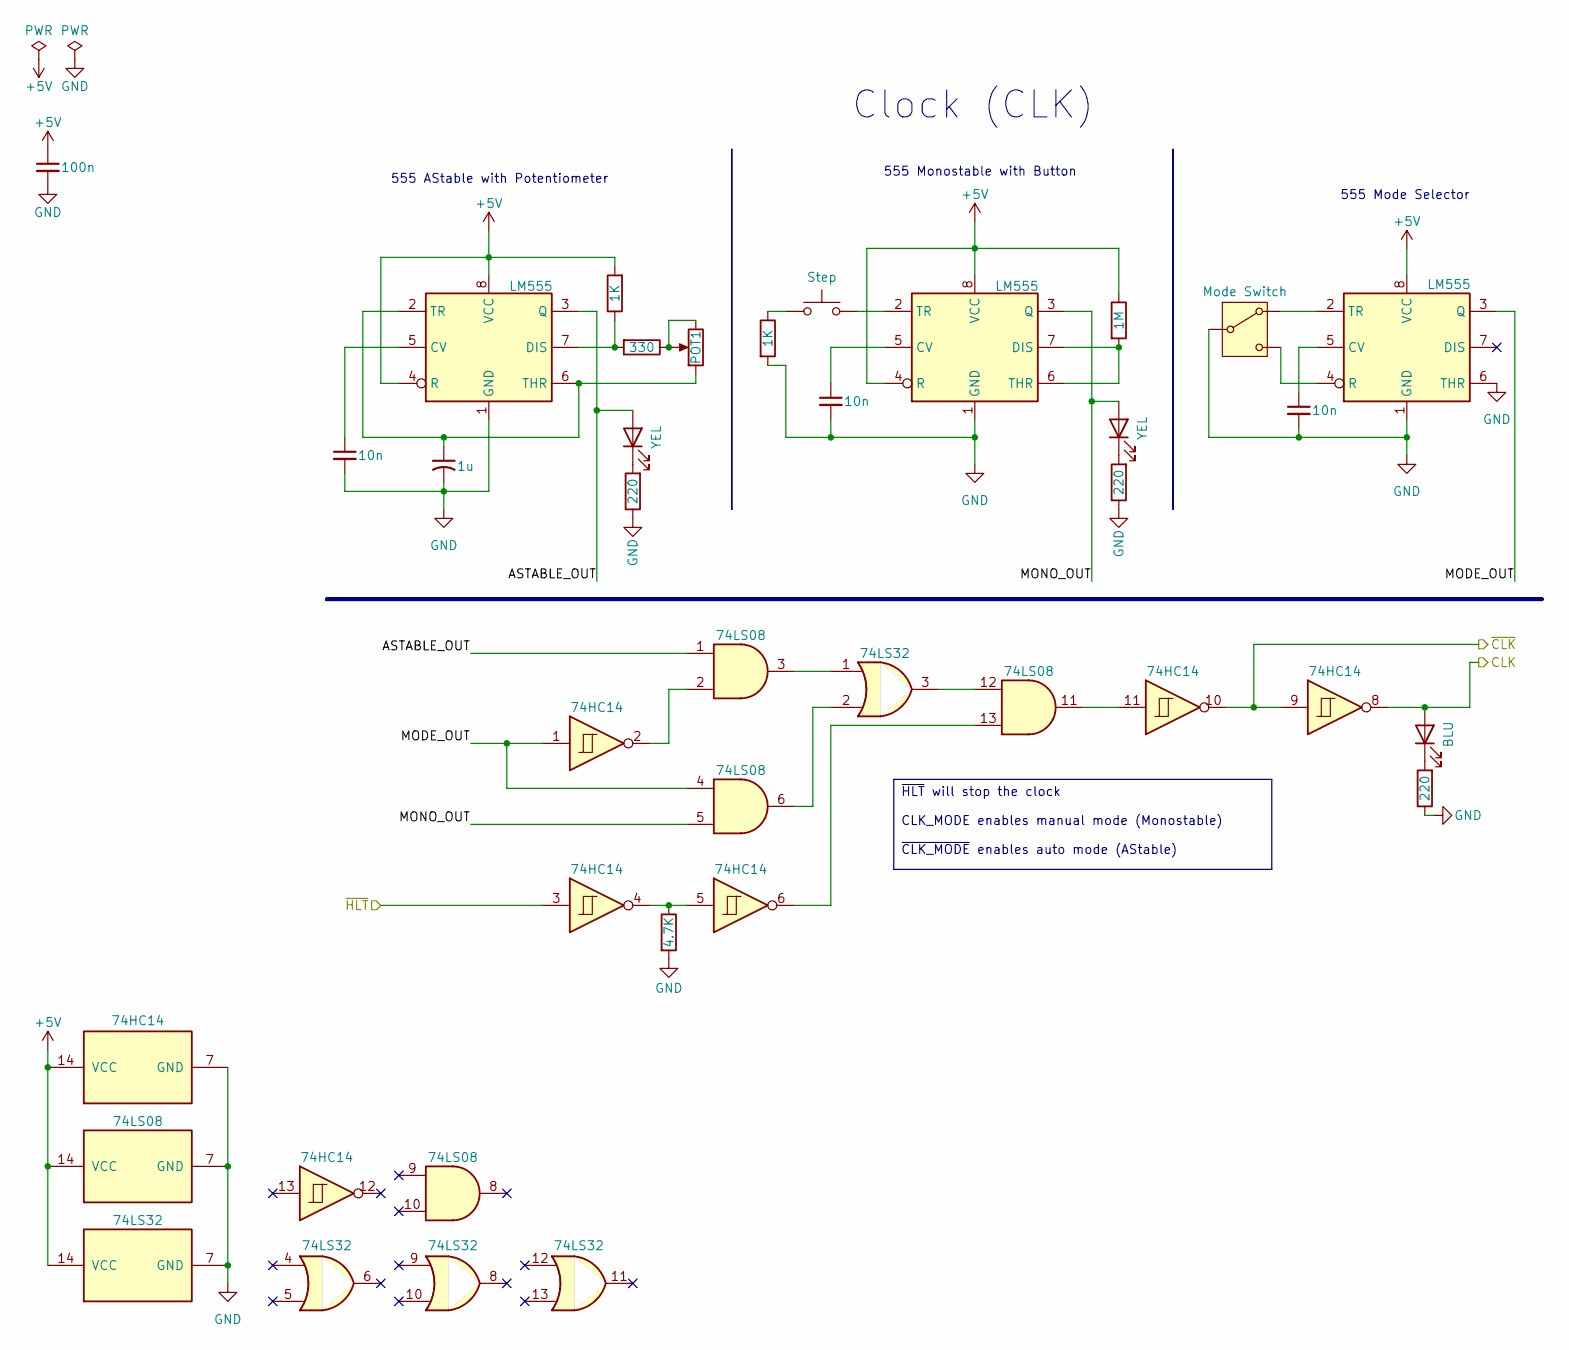
[picture p80: schematic clock.kicad_sch]

Parts:
C1: 1u; CP_Radial_D8.0mm_P5.00mm
C2, C3, C4: 10n; C_Disc_D5.0mm_W2.5mm_P5.00mm
C5: 100n; C_Disc_D5.0mm_W2.5mm_P5.00mm
D1, D3: YEL; LED_D5.0mm
D95: BLU; LED_D5.0mm
POT1: R_Potentiometer; Potentiometer_Bourns_3386P_Vertical
R1, R7, R108: 220; R_Axial_DIN0207_L6.3mm_D2.5mm_P7.62mm_Horizontal
R3, R5: 1K; R_Axial_DIN0207_L6.3mm_D2.5mm_P7.62mm_Horizontal
R4: 330; R_Axial_DIN0207_L6.3mm_D2.5mm_P7.62mm_Horizontal
R6: 1M; R_Axial_DIN0207_L6.3mm_D2.5mm_P7.62mm_Horizontal
R107: 4.7K; R_Axial_DIN0207_L6.3mm_D2.5mm_P7.62mm_Horizontal
SW2: Mode Switch; SW_SLW-883935-2A-D
SWBU1: Step; SW_PUSH_6mm
U1, U2, U20: LM555; DIP-8_W7.62mm_Socket_LongPads
U3: 74LS08; DIP-14_W7.62mm_Socket_LongPads
U17: 74HC14; DIP-14_W7.62mm_Socket_LongPads
U19: 74LS32; DIP-14_W7.62mm_Socket_LongPads

Connections:
+5V: C5.1, R3.2, R6.1, U1.4 (R), U1.8 (VCC), U2.4 (R), U2.8 (VCC), U3.14 (VCC), U17.14 (VCC), U19.14 (VCC), U20.8 (VCC)
ASTABLE_OUT: D3.2 (A), U1.3 (Q), U3.1
CLK: D95.2 (A), U17.8
GND: C1.2, C2.2, C3.2, C4.2, C5.2, R1.1, R5.2, R7.1, R107.2, R108.1, SW2.2 (B), U1.1 (GND), U2.1 (GND), U3.7 (GND), U17.7 (GND), U19.7 (GND), U20.1 (GND), U20.6 (THR)
MODE_OUT: U3.4, U17.1, U20.3 (Q)
MONO_OUT: D1.2 (A), U2.3 (Q), U3.5
unnamed: C1.1, POT1.1, U1.2 (TR), U1.6 (THR)
unnamed: C2.1, U1.5 (CV)
unnamed: C3.1, U2.5 (CV)
unnamed: C4.1, U20.5 (CV)
unnamed: D1.1 (K), R1.2
unnamed: D3.1 (K), R7.2
unnamed: D95.1 (K), R108.2
unnamed: POT1.2, POT1.3, R4.1
unnamed: R3.1, R4.2, U1.7 (DIS)
unnamed: R5.1, SWBU1.1
unnamed: R6.2, U2.6 (THR), U2.7 (DIS)
unnamed: R107.1, U17.4, U17.5
unnamed: SW2.1 (A), U20.2 (TR)
unnamed: SW2.3 (C), U20.4 (R)
unnamed: SWBU1.2, U2.2 (TR)
unnamed: U3.2, U17.2
unnamed: U3.13, U17.6
unnamed: U3.11, U17.11
unnamed: U3.3, U19.1
unnamed: U3.6, U19.2
unnamed: U3.12, U19.3
~CLK: U17.9, U17.10
~HLT: U17.3

Notes on the sheet:
555 Monostable with Button
555 AStable with Potentiometer
555 Mode Selector
Clock (CLK)
~{HLT} will stop the clock CLK_MODE enables manual mode (Monostable) ~{CLK_MODE} enables auto mode (AStable)
