kevinmfox/8-bit-computer/schematics/Main/sheets/control-unit.kicad_sch

## KiCad design schematics/Main/sheets/control-unit.kicad_sch (2026-01-15)

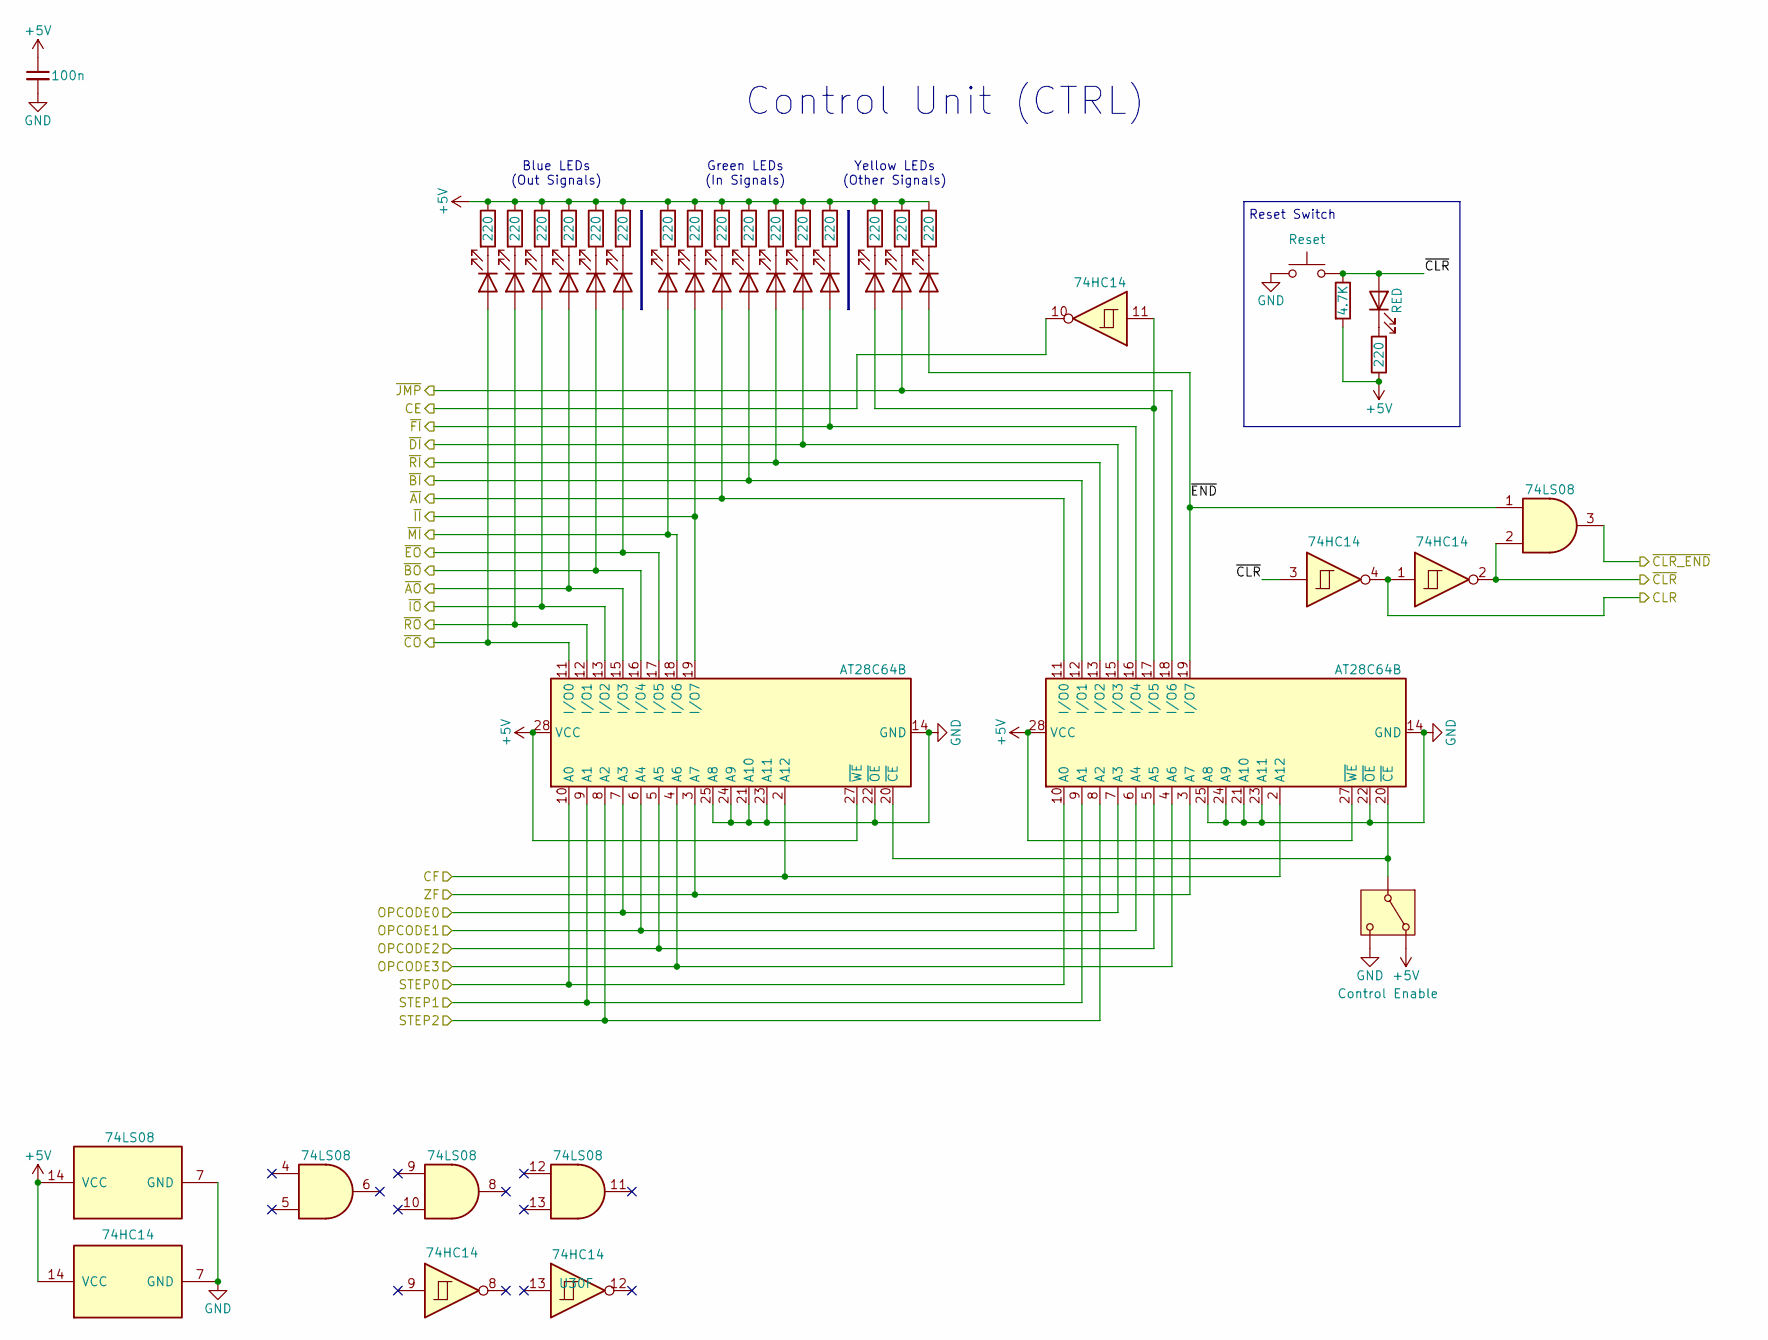
[picture p81: schematic control-unit.kicad_sch]

Parts:
C17: 100n; C_Disc_D5.0mm_W2.5mm_P5.00mm
D58: RED; LED_D5.0mm
D66, D67, D68, D69, D70, D71: BLU; LED_D5.0mm
D72, D73, D74, D75, D76, D77, D78: GRN; LED_D5.0mm
D79, D80, D81: YEL; LED_D5.0mm
R69: 4.7K; R_Axial_DIN0207_L6.3mm_D2.5mm_P7.62mm_Horizontal
R70, R77, R78, R79, R80, R81, R82, R83, R84, R85, R86, R87, R88, R89, R90, R91, R92: 220; R_Axial_DIN0207_L6.3mm_D2.5mm_P7.62mm_Horizontal
SW4: Control Enable; SW_SLW-883935-2A-D
SWBU5: Reset; SW_PUSH_6mm
U27, U28: AT28C64B; DIP-28_W15.24mm_Socket_LongPads
U29: 74LS08; DIP-14_W7.62mm_Socket_LongPads
U30: 74HC14; DIP-14_W7.62mm_Socket_LongPads

Connections:
+5V: C17.1, R69.2, R70.1, R77.1, R78.1, R79.1, R80.1, R81.1, R82.1, R83.1, R84.1, R85.1, R86.1, R87.1, R88.1, R89.1, R90.1, R91.1, R92.1, SW4.1 (A), U27.27 (~WE), U27.28 (VCC), U28.27 (~WE), U28.28 (VCC), U29.14 (VCC), U30.14 (VCC)
CE: U30.10
CF: U27.2 (A12), U28.2 (A12)
CLR: U30.1, U30.4
GND: C17.2, SW4.3 (C), SWBU5.1, U27.14 (GND), U27.21 (A10), U27.22 (~OE), U27.23 (A11), U27.24 (A9), U27.25 (A8), U28.14 (GND), U28.21 (A10), U28.22 (~OE), U28.23 (A11), U28.24 (A9), U28.25 (A8), U29.7 (GND), U30.7 (GND)
unnamed: D58.1 (K), R70.2
unnamed: D66.1 (K), R77.2
unnamed: D67.1 (K), R78.2
unnamed: D68.1 (K), R79.2
unnamed: D69.1 (K), R80.2
unnamed: D70.1 (K), R81.2
unnamed: D71.1 (K), R82.2
unnamed: D72.1 (K), R83.2
unnamed: D73.1 (K), R84.2
unnamed: D74.1 (K), R85.2
unnamed: D75.1 (K), R86.2
unnamed: D76.1 (K), R87.2
unnamed: D77.1 (K), R88.2
unnamed: D78.1 (K), R89.2
unnamed: D79.1 (K), R90.2
unnamed: D80.1 (K), R91.2
unnamed: D81.1 (K), R92.2
unnamed: D81.2 (A), U27.17 (I/O5), U30.11
unnamed: SW4.2 (B), U27.20 (~CE), U28.20 (~CE)
OPCODE0: U27.7 (A3), U28.7 (A3)
OPCODE1: U27.6 (A4), U28.6 (A4)
OPCODE2: U27.5 (A5), U28.5 (A5)
OPCODE3: U27.4 (A6), U28.4 (A6)
STEP0: U27.10 (A0), U28.10 (A0)
STEP1: U27.9 (A1), U28.9 (A1)
STEP2: U27.8 (A2), U28.8 (A2)
ZF: U27.3 (A7), U28.3 (A7)
~AI: D76.2 (A), U27.11 (I/O0)
~AO: D68.2 (A), U28.15 (I/O3)
~BI: D75.2 (A), U27.12 (I/O1)
~BO: D67.2 (A), U28.16 (I/O4)
~CLR_END: U29.3
~CLR: D58.2 (A), R69.1, SWBU5.2, U29.2, U30.2, U30.3
~CO: D71.2 (A), U28.11 (I/O0)
~DI: D73.2 (A), U27.15 (I/O3)
~END: D79.2 (A), U27.19 (I/O7), U29.1
~EO: D66.2 (A), U28.17 (I/O5)
~FI: D72.2 (A), U27.16 (I/O4)
~II: D77.2 (A), U28.19 (I/O7)
~IO: D69.2 (A), U28.13 (I/O2)
~JMP: D80.2 (A), U27.18 (I/O6)
~MI: D78.2 (A), U28.18 (I/O6)
~RI: D74.2 (A), U27.13 (I/O2)
~RO: D70.2 (A), U28.12 (I/O1)

Notes on the sheet:
Control Unit (CTRL)
Reset Switch
Yellow LEDs (Other Signals)
Blue LEDs (Out Signals)
Green LEDs (In Signals)
