kevinmfox/8-bit-computer/schematics/Main/sheets/display.kicad_sch

## KiCad design schematics/Main/sheets/display.kicad_sch (2026-01-15)

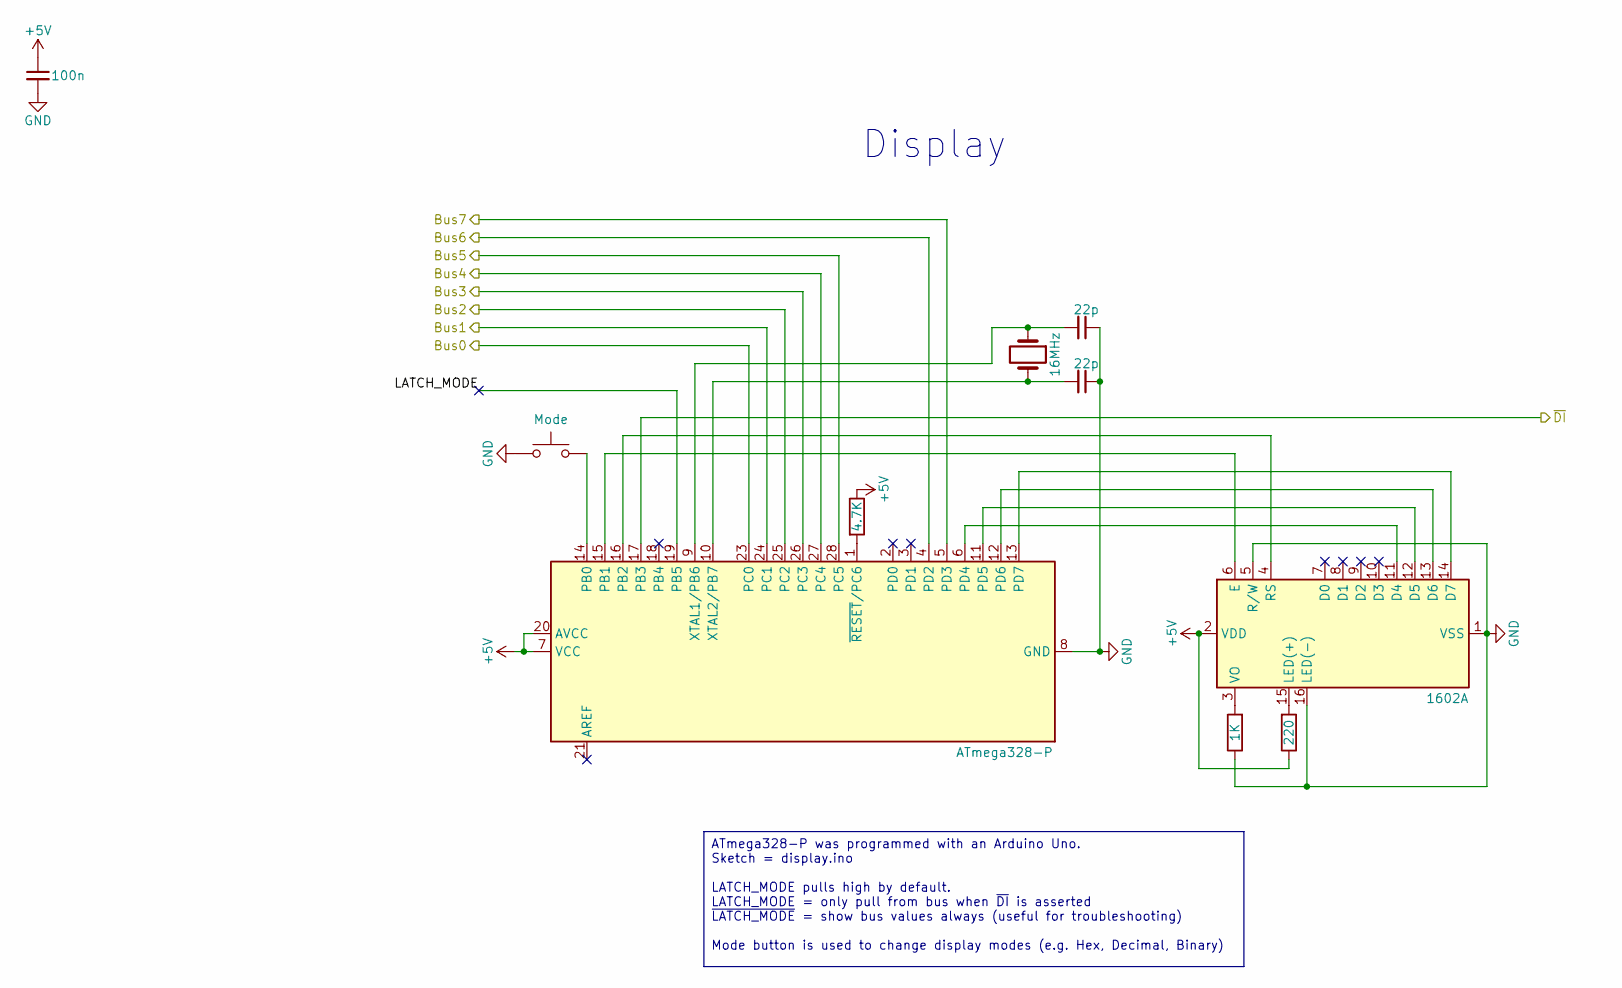
[picture p82: schematic display.kicad_sch]

Parts:
C11: 100n; C_Disc_D5.0mm_W2.5mm_P5.00mm
C12, C13: 22p; C_Disc_D5.0mm_W2.5mm_P5.00mm
DS1: 1602A; WC1602A
R43: 4.7K; R_Axial_DIN0207_L6.3mm_D2.5mm_P7.62mm_Horizontal
R44: 1K; R_Axial_DIN0207_L6.3mm_D2.5mm_P7.62mm_Horizontal
R45: 220; R_Axial_DIN0207_L6.3mm_D2.5mm_P7.62mm_Horizontal
SWBU3: Mode; SW_PUSH_6mm
U15: ATmega328-P; DIP-28_W7.62mm_Socket_LongPads
Y1: 16MHz; Crystal_HC49-U_Vertical

Connections:
+5V: C11.1, DS1.2 (VDD), R43.1, R45.1, U15.7 (VCC), U15.20 (AVCC)
Bus0: U15.23 (PC0)
Bus1: U15.24 (PC1)
Bus2: U15.25 (PC2)
Bus3: U15.26 (PC3)
Bus4: U15.27 (PC4)
Bus5: U15.28 (PC5)
Bus6: U15.4 (PD2)
Bus7: U15.5 (PD3)
GND: C11.2, C12.1, C13.1, DS1.1 (VSS), DS1.5 (R/W), DS1.16 (LED(-)), R44.1, SWBU3.1, U15.8 (GND), U15.22 (GND)
LATCH_MODE: U15.19 (PB5)
unnamed: C12.2, U15.9 (XTAL1/PB6), Y1.1
unnamed: C13.2, U15.10 (XTAL2/PB7), Y1.2
unnamed: DS1.3 (VO), R44.2
unnamed: DS1.4 (RS), U15.16 (PB2)
unnamed: DS1.6 (E), U15.15 (PB1)
unnamed: DS1.11 (D4), U15.6 (PD4)
unnamed: DS1.12 (D5), U15.11 (PD5)
unnamed: DS1.13 (D6), U15.12 (PD6)
unnamed: DS1.14 (D7), U15.13 (PD7)
unnamed: DS1.15 (LED(+)), R45.2
unnamed: R43.2, U15.1 (~RESET/PC6)
unnamed: SWBU3.2, U15.14 (PB0)
~DI: U15.17 (PB3)

Notes on the sheet:
Display
ATmega328-P was programmed with an Arduino Uno. Sketch = display.ino LATCH_MODE pulls high by default. LATCH_MODE = only pull from bus when ~{DI} is asserted ~{LATCH_MODE} = show bus values always (useful for troubleshooting) Mode button is used to change display modes (e.g. Hex, Decimal, Binary)
