kevinmfox/8-bit-computer/schematics/Main/sheets/flags-register.kicad_sch

## KiCad design schematics/Main/sheets/flags-register.kicad_sch (2026-01-15)

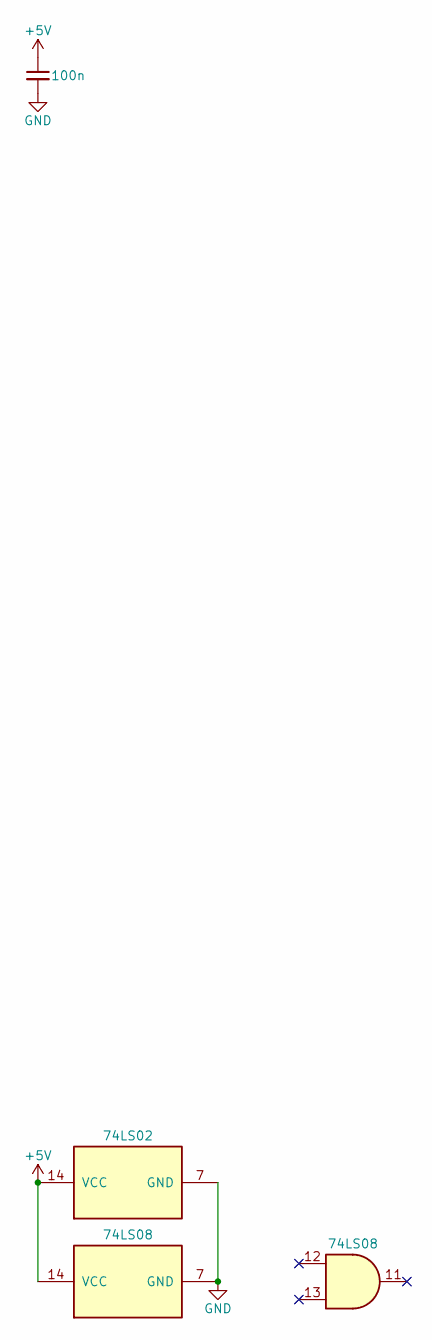
[picture p83: schematic flags-register.kicad_sch]

Parts:
C18: 100n
U37: 74LS02
U38: 74LS08

Connections:
+5V: C18.1, U37.14 (VCC), U38.14 (VCC)
GND: C18.2, U37.7 (GND), U38.7 (GND)
