kevinmfox/8-bit-computer/schematics/Main/sheets/ir.kicad_sch

## KiCad design schematics/Main/sheets/ir.kicad_sch (2026-01-15)

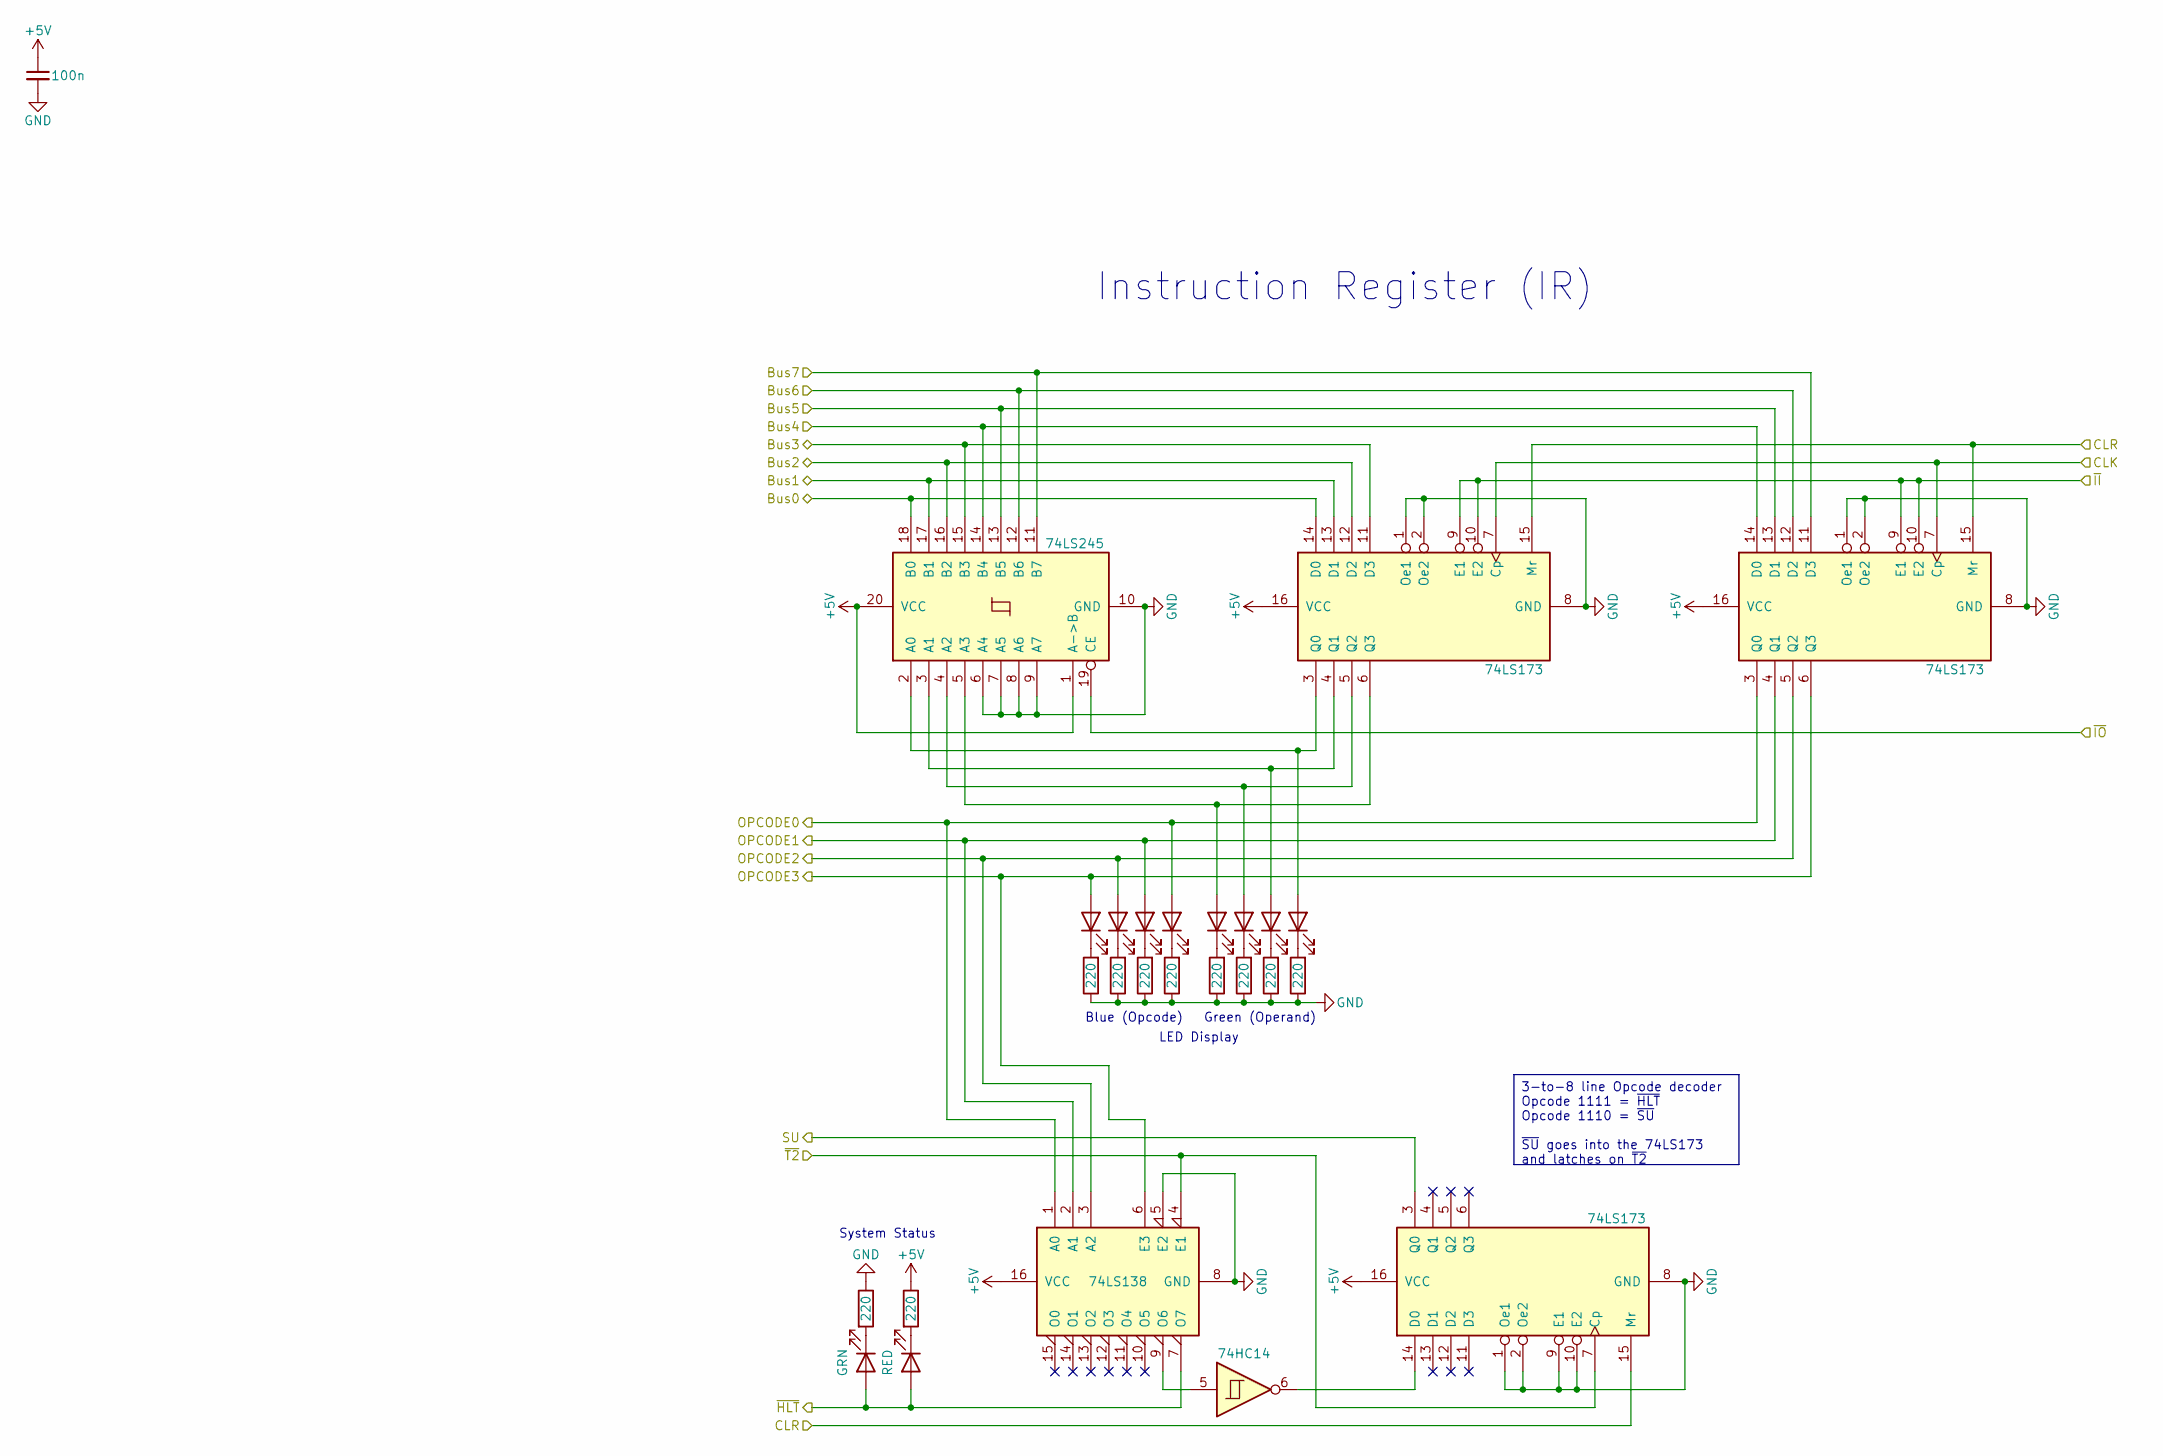
[picture p84: schematic ir.kicad_sch]

Parts:
C15: 100n; C_Disc_D5.0mm_W2.5mm_P5.00mm
D44, D45, D46, D47: BLU; LED_D5.0mm
D48, D49, D50, D51, D94: GRN; LED_D5.0mm
D93: RED; LED_D5.0mm
R54, R55, R56, R57, R58, R59, R60, R61, R105, R106: 220; R_Axial_DIN0207_L6.3mm_D2.5mm_P7.62mm_Horizontal
U22: 74LS245; DIP-22_W7.62mm_Socket_LongPads
U23, U24, U40: 74LS173; DIP-16_W7.62mm_Socket_LongPads
U30: 74HC14; DIP-14_W7.62mm_Socket_LongPads
U39: 74LS138; DIP-16_W7.62mm_Socket_LongPads

Connections:
+5V: C15.1, R105.1, U22.1 (A->B), U22.20 (VCC), U23.16 (VCC), U24.16 (VCC), U39.16 (VCC), U40.16 (VCC)
Bus0: U22.18 (B0), U23.14 (D0)
Bus1: U22.17 (B1), U23.13 (D1)
Bus2: U22.16 (B2), U23.12 (D2)
Bus3: U22.15 (B3), U23.11 (D3)
Bus4: U22.14 (B4), U24.14 (D0)
Bus5: U22.13 (B5), U24.13 (D1)
Bus6: U22.12 (B6), U24.12 (D2)
Bus7: U22.11 (B7), U24.11 (D3)
CLK: U23.7 (Cp), U24.7 (Cp)
CLR: U23.15 (Mr), U24.15 (Mr), U40.15 (Mr)
GND: C15.2, R54.1, R55.1, R56.1, R57.1, R58.1, R59.1, R60.1, R61.1, R106.1, U22.6 (A4), U22.7 (A5), U22.8 (A6), U22.9 (A7), U22.10 (GND), U23.1 (Oe1), U23.2 (Oe2), U23.8 (GND), U24.1 (Oe1), U24.2 (Oe2), U24.8 (GND), U39.5 (E2), U39.8 (GND), U40.1 (Oe1), U40.2 (Oe2), U40.8 (GND), U40.9 (E1), U40.10 (E2)
unnamed: D44.1 (K), R54.2
unnamed: D45.1 (K), R55.2
unnamed: D46.1 (K), R56.2
unnamed: D47.1 (K), R57.2
unnamed: D48.1 (K), R58.2
unnamed: D48.2 (A), U22.5 (A3), U23.6 (Q3)
unnamed: D49.1 (K), R59.2
unnamed: D49.2 (A), U22.4 (A2), U23.5 (Q2)
unnamed: D50.1 (K), R60.2
unnamed: D50.2 (A), U22.3 (A1), U23.4 (Q1)
unnamed: D51.1 (K), R61.2
unnamed: D51.2 (A), U22.2 (A0), U23.3 (Q0)
unnamed: D93.1 (K), R105.2
unnamed: D94.1 (K), R106.2
unnamed: U30.5, U39.9 (O6)
unnamed: U30.6, U40.14 (D0)
OPCODE0: D47.2 (A), U24.3 (Q0), U39.1 (A0)
OPCODE1: D46.2 (A), U24.4 (Q1), U39.2 (A1)
OPCODE2: D45.2 (A), U24.5 (Q2), U39.3 (A2)
OPCODE3: D44.2 (A), U24.6 (Q3), U39.6 (E3)
SU: U40.3 (Q0)
~HLT: D93.2 (A), D94.2 (A), U39.7 (O7)
~II: U23.9 (E1), U23.10 (E2), U24.9 (E1), U24.10 (E2)
~IO: U22.19 (CE)
~T2: U39.4 (E1), U40.7 (Cp)

Notes on the sheet:
Blue (Opcode)
Green (Operand)
LED Display
Instruction Register (IR)
System Status
3-to-8 line Opcode decoder Opcode 1111 = ~{HLT} Opcode 1110 = ~{SU} ~{SU} goes into the 74LS173 and latches on ~{T2}
