kevinmfox/8-bit-computer/schematics/Main/sheets/mar.kicad_sch

## KiCad design schematics/Main/sheets/mar.kicad_sch (2026-01-15)

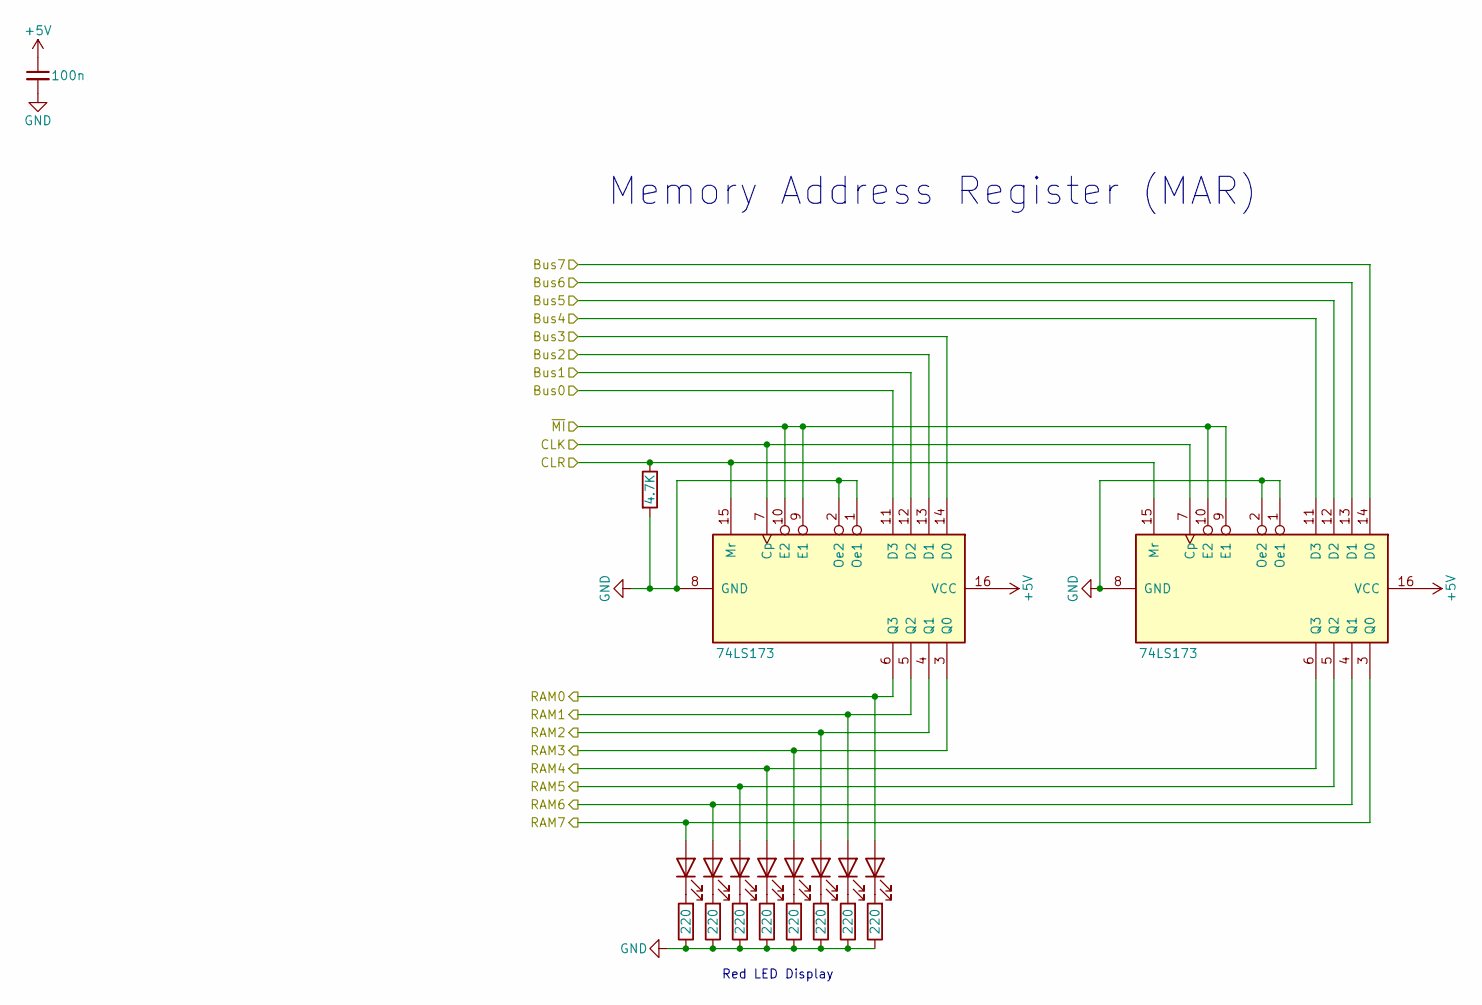
[picture p85: schematic mar.kicad_sch]

Parts:
C7: 100n; C_Disc_D5.0mm_W2.5mm_P5.00mm
D12, D13, D14, D15, D16, D17, D18, D19: RED; LED_D5.0mm
R17: 4.7K; R_Axial_DIN0207_L6.3mm_D2.5mm_P7.62mm_Horizontal
R18, R19, R20, R21, R22, R23, R24, R25: 220; R_Axial_DIN0207_L6.3mm_D2.5mm_P7.62mm_Horizontal
U7, U8: 74LS173; DIP-16_W7.62mm_Socket_LongPads

Connections:
+5V: C7.1, U7.16 (VCC), U8.16 (VCC)
Bus0: U7.11 (D3)
Bus1: U7.12 (D2)
Bus2: U7.13 (D1)
Bus3: U7.14 (D0)
Bus4: U8.11 (D3)
Bus5: U8.12 (D2)
Bus6: U8.13 (D1)
Bus7: U8.14 (D0)
CLK: U7.7 (Cp), U8.7 (Cp)
CLR: R17.1, U7.15 (Mr), U8.15 (Mr)
GND: C7.2, R17.2, R18.1, R19.1, R20.1, R21.1, R22.1, R23.1, R24.1, R25.1, U7.1 (Oe1), U7.2 (Oe2), U7.8 (GND), U8.1 (Oe1), U8.2 (Oe2), U8.8 (GND)
unnamed: D12.1 (K), R18.2
unnamed: D13.1 (K), R19.2
unnamed: D14.1 (K), R20.2
unnamed: D15.1 (K), R21.2
unnamed: D16.1 (K), R22.2
unnamed: D17.1 (K), R23.2
unnamed: D18.1 (K), R24.2
unnamed: D19.1 (K), R25.2
RAM0: D12.2 (A), U7.6 (Q3)
RAM1: D13.2 (A), U7.5 (Q2)
RAM2: D14.2 (A), U7.4 (Q1)
RAM3: D15.2 (A), U7.3 (Q0)
RAM4: D16.2 (A), U8.6 (Q3)
RAM5: D17.2 (A), U8.5 (Q2)
RAM6: D18.2 (A), U8.4 (Q1)
RAM7: D19.2 (A), U8.3 (Q0)
~MI: U7.9 (E1), U7.10 (E2), U8.9 (E1), U8.10 (E2)

Notes on the sheet:
Memory Address Register (MAR)
Red LED Display
