kevinmfox/8-bit-computer/schematics/Main/sheets/microstep-counter.kicad_sch

## KiCad design schematics/Main/sheets/microstep-counter.kicad_sch (2026-01-15)

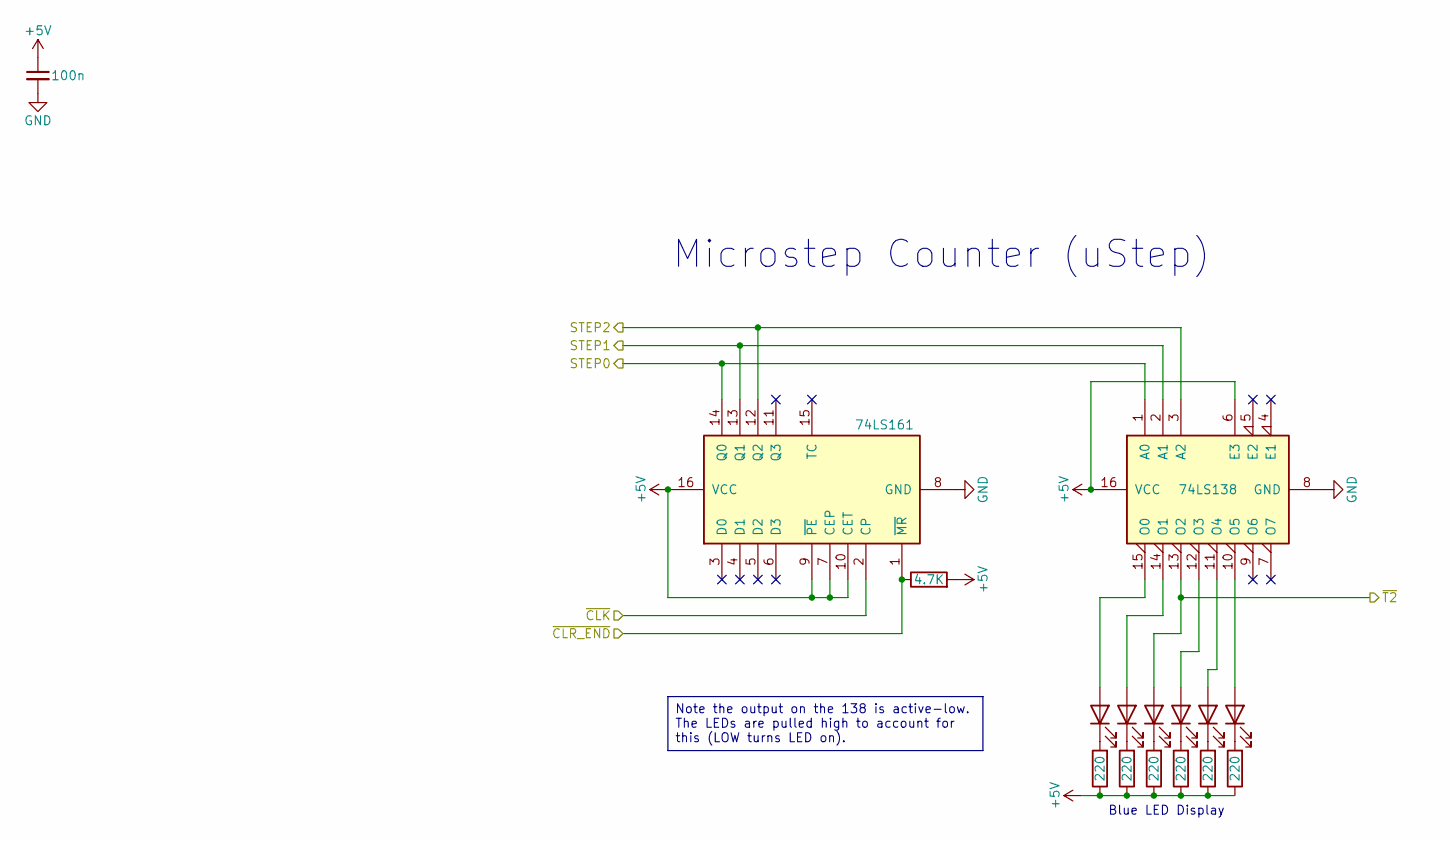
[picture p86: schematic microstep-counter.kicad_sch]

Parts:
C16: 100n; C_Disc_D5.0mm_W2.5mm_P5.00mm
D52, D53, D54, D55, D56, D57: BLU; LED_D5.0mm
R62: 4.7K; R_Axial_DIN0207_L6.3mm_D2.5mm_P7.62mm_Horizontal
R63, R64, R65, R66, R67, R68: 220; R_Axial_DIN0207_L6.3mm_D2.5mm_P7.62mm_Horizontal
U25: 74LS161; DIP-16_W7.62mm_Socket_LongPads
U26: 74LS138; DIP-16_W7.62mm_Socket_LongPads

Connections:
+5V: C16.1, R62.2, R63.1, R64.1, R65.1, R66.1, R67.1, R68.1, U25.7 (CEP), U25.9 (~PE), U25.10 (CET), U25.16 (VCC), U26.6 (E3), U26.16 (VCC)
GND: C16.2, U25.8 (GND), U26.8 (GND)
unnamed: D52.1 (K), R63.2
unnamed: D52.2 (A), U26.15 (O0)
unnamed: D53.1 (K), R64.2
unnamed: D53.2 (A), U26.14 (O1)
unnamed: D54.1 (K), R65.2
unnamed: D55.1 (K), R66.2
unnamed: D55.2 (A), U26.12 (O3)
unnamed: D56.1 (K), R67.2
unnamed: D56.2 (A), U26.11 (O4)
unnamed: D57.1 (K), R68.2
unnamed: D57.2 (A), U26.10 (O5)
STEP0: U25.14 (Q0), U26.1 (A0)
STEP1: U25.13 (Q1), U26.2 (A1)
STEP2: U25.12 (Q2), U26.3 (A2)
~CLK: U25.2 (CP)
~CLR_END: R62.1, U25.1 (~MR)
~T2: D54.2 (A), U26.13 (O2)

Notes on the sheet:
Microstep Counter (uStep)
Blue LED Display
Note the output on the 138 is active-low. The LEDs are pulled high to account for this (LOW turns LED on).
