kevinmfox/8-bit-computer/schematics/Main/sheets/program-counter.kicad_sch

## KiCad design schematics/Main/sheets/program-counter.kicad_sch (2026-01-15)

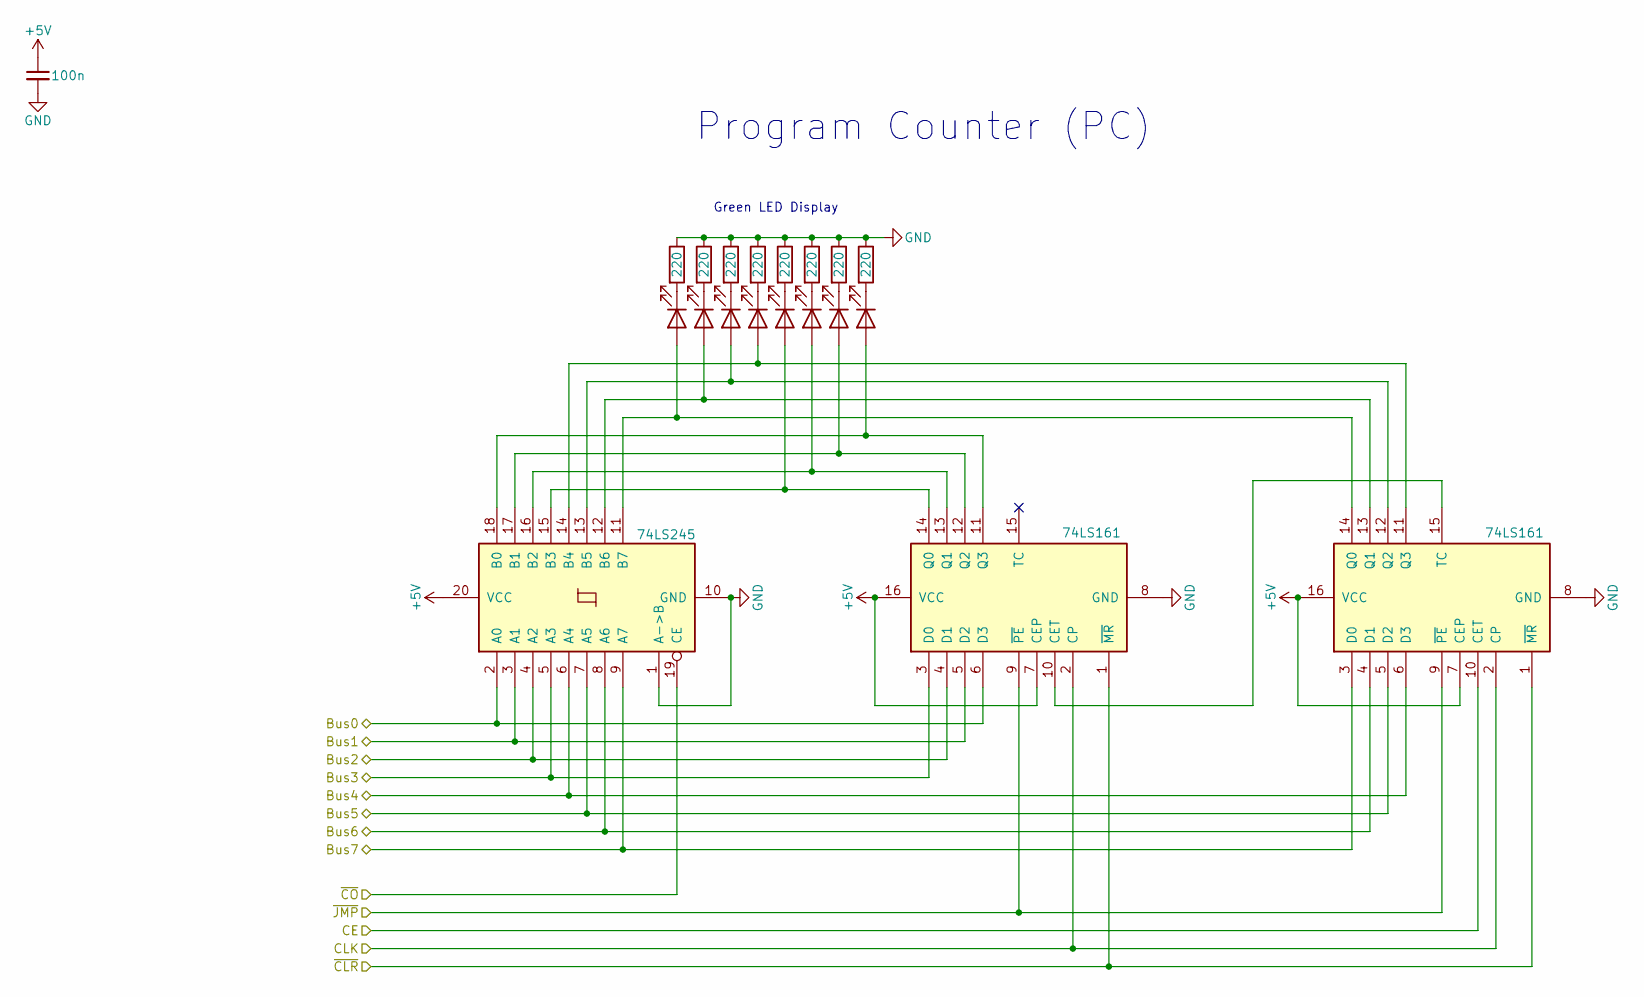
[picture p87: schematic program-counter.kicad_sch]

Parts:
C6: 100n; C_Disc_D5.0mm_W2.5mm_P5.00mm
D4, D5, D6, D7, D8, D9, D10, D11: GRN; LED_D5.0mm
R9, R10, R11, R12, R13, R14, R15, R16: 220; R_Axial_DIN0207_L6.3mm_D2.5mm_P7.62mm_Horizontal
U4: 74LS245; DIP-22_W7.62mm_Socket_LongPads
U5, U6: 74LS161; DIP-16_W7.62mm_Socket_LongPads

Connections:
+5V: C6.1, U4.20 (VCC), U5.7 (CEP), U5.16 (VCC), U6.7 (CEP), U6.16 (VCC)
Bus0: U4.2 (A0), U5.6 (D3)
Bus1: U4.3 (A1), U5.5 (D2)
Bus2: U4.4 (A2), U5.4 (D1)
Bus3: U4.5 (A3), U5.3 (D0)
Bus4: U4.6 (A4), U6.6 (D3)
Bus5: U4.7 (A5), U6.5 (D2)
Bus6: U4.8 (A6), U6.4 (D1)
Bus7: U4.9 (A7), U6.3 (D0)
CE: U6.10 (CET)
CLK: U5.2 (CP), U6.2 (CP)
GND: C6.2, R9.1, R10.1, R11.1, R12.1, R13.1, R14.1, R15.1, R16.1, U4.1 (A->B), U4.10 (GND), U5.8 (GND), U6.8 (GND)
unnamed: D4.1 (K), R9.2
unnamed: D4.2 (A), U4.11 (B7), U6.14 (Q0)
unnamed: D5.1 (K), R10.2
unnamed: D5.2 (A), U4.12 (B6), U6.13 (Q1)
unnamed: D6.1 (K), R11.2
unnamed: D6.2 (A), U4.13 (B5), U6.12 (Q2)
unnamed: D7.1 (K), R12.2
unnamed: D7.2 (A), U4.14 (B4), U6.11 (Q3)
unnamed: D8.1 (K), R13.2
unnamed: D8.2 (A), U4.15 (B3), U5.14 (Q0)
unnamed: D9.1 (K), R14.2
unnamed: D9.2 (A), U4.16 (B2), U5.13 (Q1)
unnamed: D10.1 (K), R15.2
unnamed: D10.2 (A), U4.17 (B1), U5.12 (Q2)
unnamed: D11.1 (K), R16.2
unnamed: D11.2 (A), U4.18 (B0), U5.11 (Q3)
unnamed: U5.10 (CET), U6.15 (TC)
~CLR: U5.1 (~MR), U6.1 (~MR)
~CO: U4.19 (CE)
~JMP: U5.9 (~PE), U6.9 (~PE)

Notes on the sheet:
Green LED Display
Program Counter (PC)
