kevinmfox/8-bit-computer/schematics/Main/sheets/ram.kicad_sch

## KiCad design schematics/Main/sheets/ram.kicad_sch (2026-01-15)

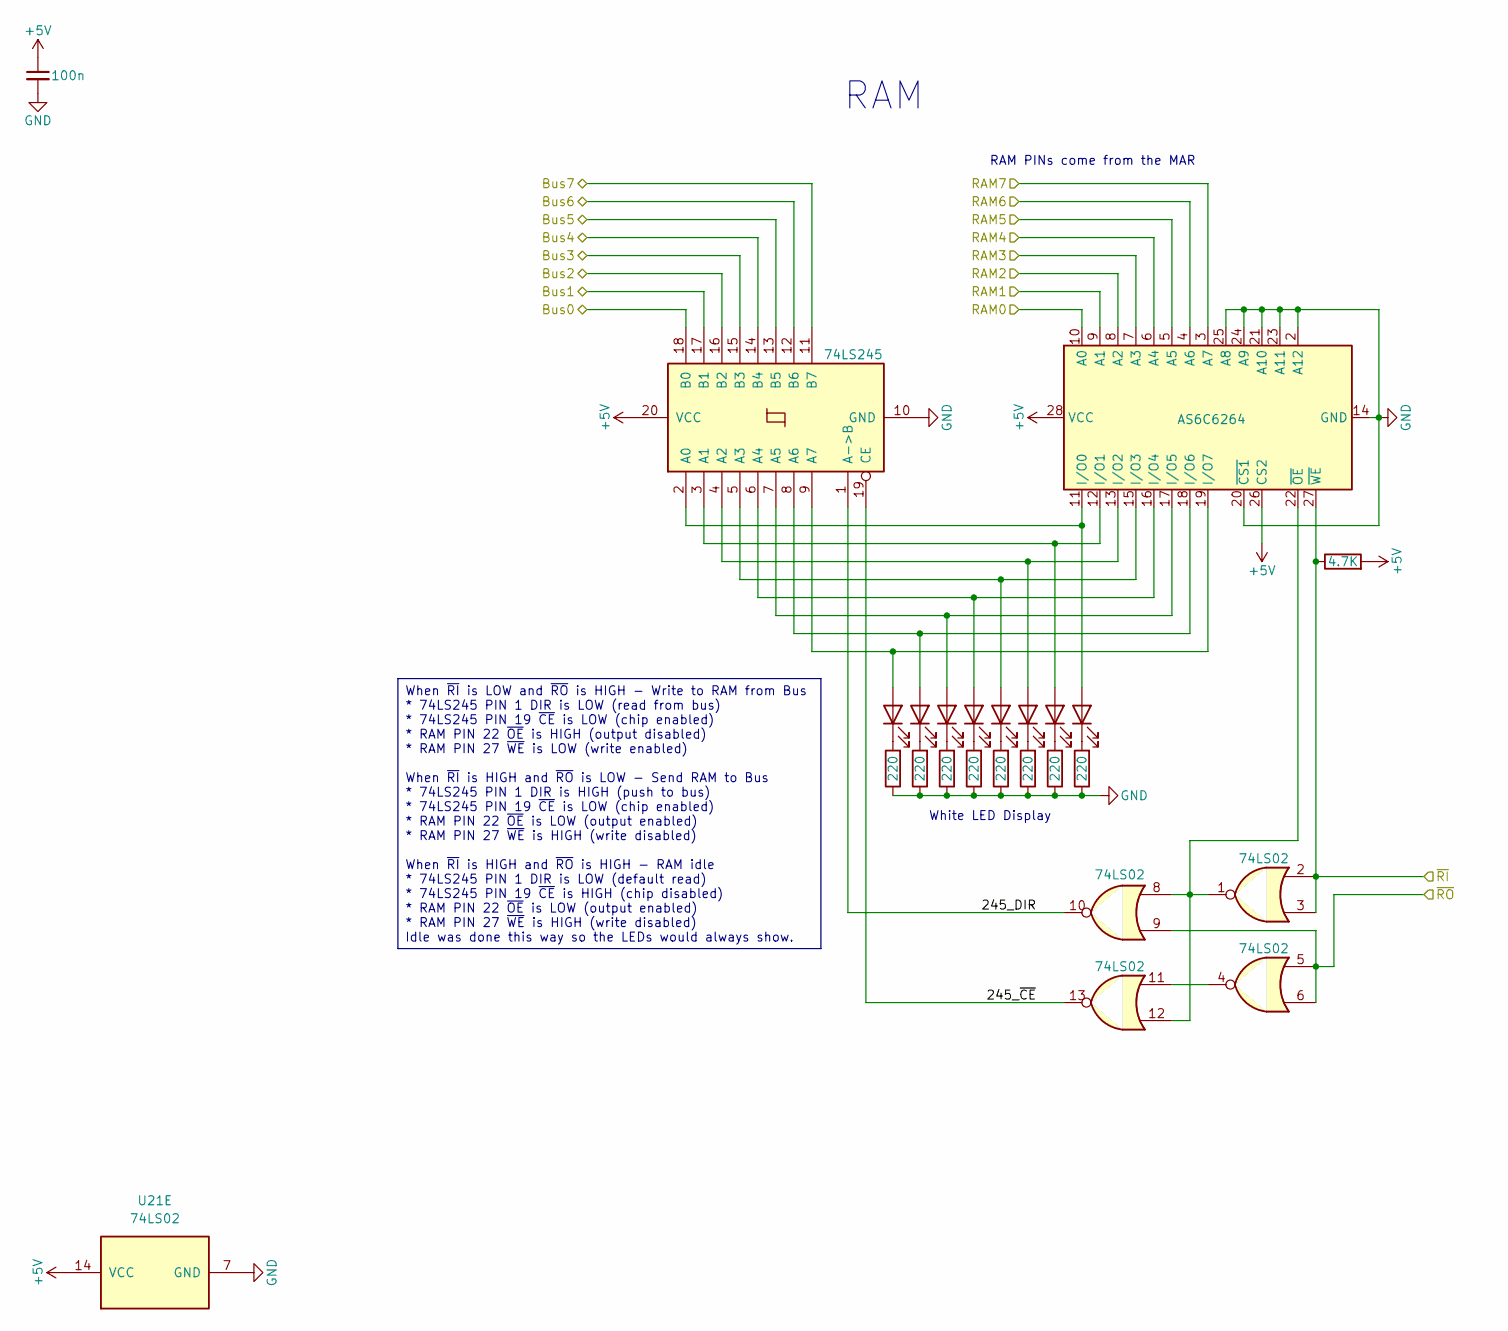
[picture p88: schematic ram.kicad_sch]

Parts:
C14: 100n; C_Disc_D5.0mm_W2.5mm_P5.00mm
D36, D37, D38, D39, D40, D41, D42, D43: WHT; LED_D5.0mm
R42: 4.7K; R_Axial_DIN0207_L6.3mm_D2.5mm_P7.62mm_Horizontal
R46, R47, R48, R49, R50, R51, R52, R53: 220; R_Axial_DIN0207_L6.3mm_D2.5mm_P7.62mm_Horizontal
U16: 74LS245; DIP-22_W7.62mm_Socket_LongPads
U18: AS6C6264; DIP-28_W15.24mm_Socket_LongPads
U21: 74LS02; DIP-14_W7.62mm_Socket_LongPads

Connections:
245_DIR: U16.1 (A->B), U21.10
245_~CE: U16.19 (CE), U21.13
+5V: C14.1, R42.2, U16.20 (VCC), U18.26 (CS2), U18.28 (VCC), U21.14 (VCC)
Bus0: U16.18 (B0)
Bus1: U16.17 (B1)
Bus2: U16.16 (B2)
Bus3: U16.15 (B3)
Bus4: U16.14 (B4)
Bus5: U16.13 (B5)
Bus6: U16.12 (B6)
Bus7: U16.11 (B7)
GND: C14.2, R46.1, R47.1, R48.1, R49.1, R50.1, R51.1, R52.1, R53.1, U16.10 (GND), U18.2 (A12), U18.14 (GND), U18.20 (~CS1), U18.21 (A10), U18.23 (A11), U18.24 (A9), U18.25 (A8), U21.7 (GND)
unnamed: D36.1 (K), R46.2
unnamed: D36.2 (A), U16.9 (A7), U18.19 (I/O7)
unnamed: D37.1 (K), R47.2
unnamed: D37.2 (A), U16.8 (A6), U18.18 (I/O6)
unnamed: D38.1 (K), R48.2
unnamed: D38.2 (A), U16.7 (A5), U18.17 (I/O5)
unnamed: D39.1 (K), R49.2
unnamed: D39.2 (A), U16.6 (A4), U18.16 (I/O4)
unnamed: D40.1 (K), R50.2
unnamed: D40.2 (A), U16.5 (A3), U18.15 (I/O3)
unnamed: D41.1 (K), R51.2
unnamed: D41.2 (A), U16.4 (A2), U18.13 (I/O2)
unnamed: D42.1 (K), R52.2
unnamed: D42.2 (A), U16.3 (A1), U18.12 (I/O1)
unnamed: D43.1 (K), R53.2
unnamed: D43.2 (A), U16.2 (A0), U18.11 (I/O0)
unnamed: U18.22 (~OE), U21.1, U21.8, U21.12
unnamed: U21.4, U21.11
RAM0: U18.10 (A0)
RAM1: U18.9 (A1)
RAM2: U18.8 (A2)
RAM3: U18.7 (A3)
RAM4: U18.6 (A4)
RAM5: U18.5 (A5)
RAM6: U18.4 (A6)
RAM7: U18.3 (A7)
~RI: R42.1, U18.27 (~WE), U21.2, U21.3
~RO: U21.5, U21.6, U21.9

Notes on the sheet:
RAM
White LED Display
RAM PINs come from the MAR
When ~{RI} is LOW and ~{RO} is HIGH - Write to RAM from Bus * 74LS245 PIN 1 DIR is LOW (read from bus) * 74LS245 PIN 19 ~{CE} is LOW (chip enabled) * RAM PIN 22 ~{OE} is HIGH (output disabled) * RAM PIN 27 ~{WE} is LOW (write enabled) When ~{RI} is HIGH and ~{RO} is LOW - Send RAM to Bus * 74LS245 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
